lthimx/pnpbox1/freecad/magnet_support_main_arm/Capture d’écran du 2022-05-14 17-08-01.png

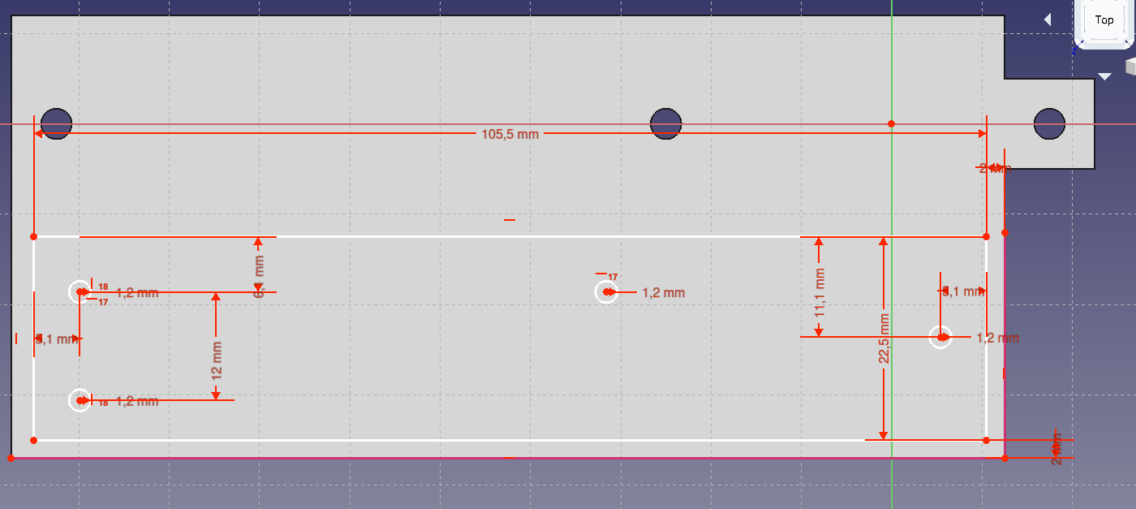
freecad/magnet_support_main_arm/Capture d’écran du 2022-05-14 17-08-01.png
