lthimx/pnpbox1/images/Capture d’écran du 2022-02-01 20-31-52.png

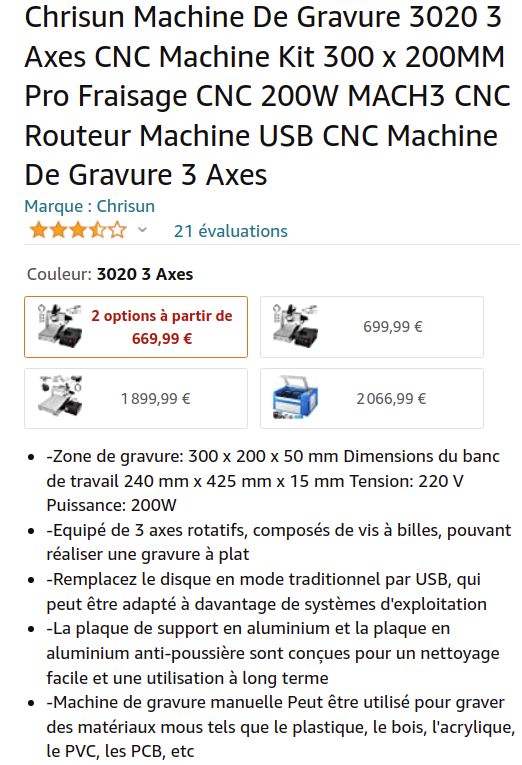
images/Capture d’écran du 2022-02-01 20-31-52.png
