lthimx/pnpbox1/openpnp/fidloc_template_18089185766861298502.png

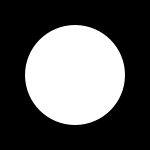
openpnp/fidloc_template_18089185766861298502.png
