lthimx/pnpbox1/freecad/magnet_support_main_arm/down_right_magnet_support_angle_arm.obj

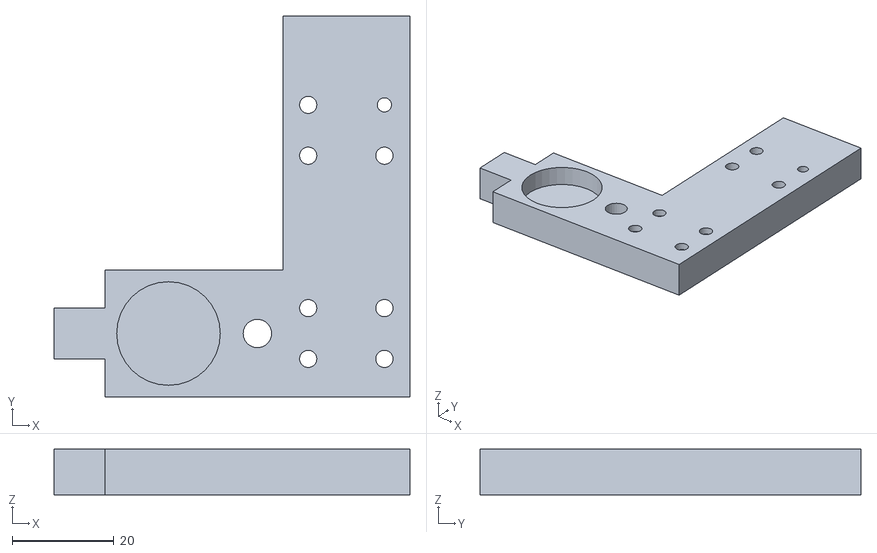
[picture p30: CAD file, 2022-06-12]
freecad/magnet_support_main_arm/down_right_magnet_support_angle_arm.obj
70.0 x 75.0 x 9.00
