lthimx/pnpbox1/freecad/reset_button/reset_unlock.obj

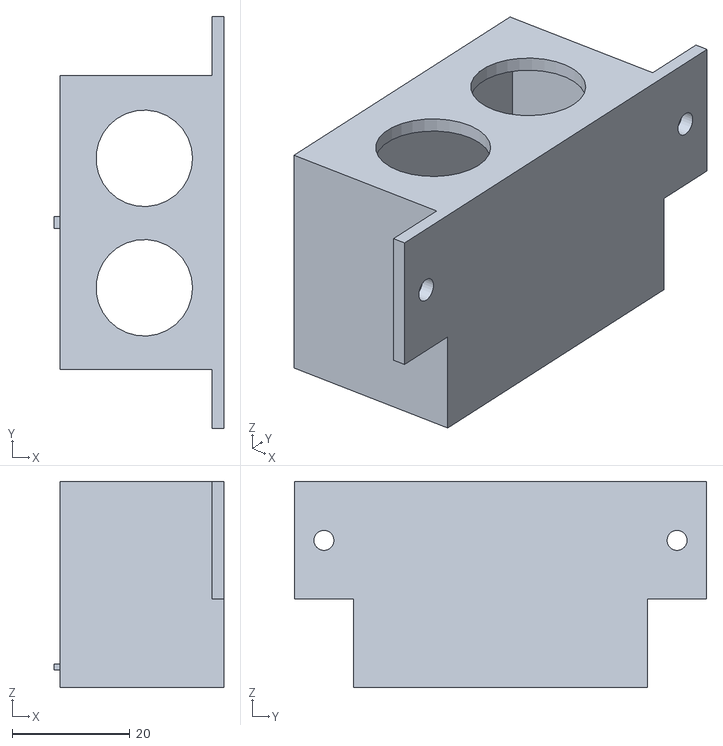
[picture p31: CAD file, 2022-04-11]
freecad/reset_button/reset_unlock.obj
28.8 x 70.0 x 35.0
