lthimx/pnpbox1/freecad/stl/acrylic_head_pnp_2.FCStd

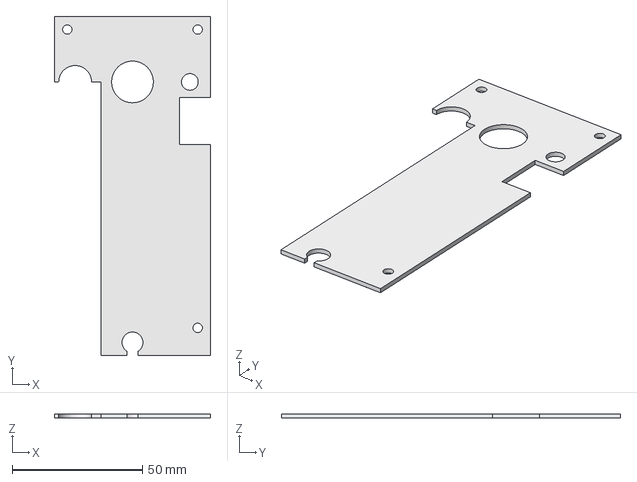
[picture p32: CAD file, 2022-04-11]
freecad/stl/acrylic_head_pnp_2.FCStd
60.0 x 130.0 x 1.60 mm
