lthimx/pnpbox1/freecad/usb_cam_case/usb_cam_case_up.FCStd

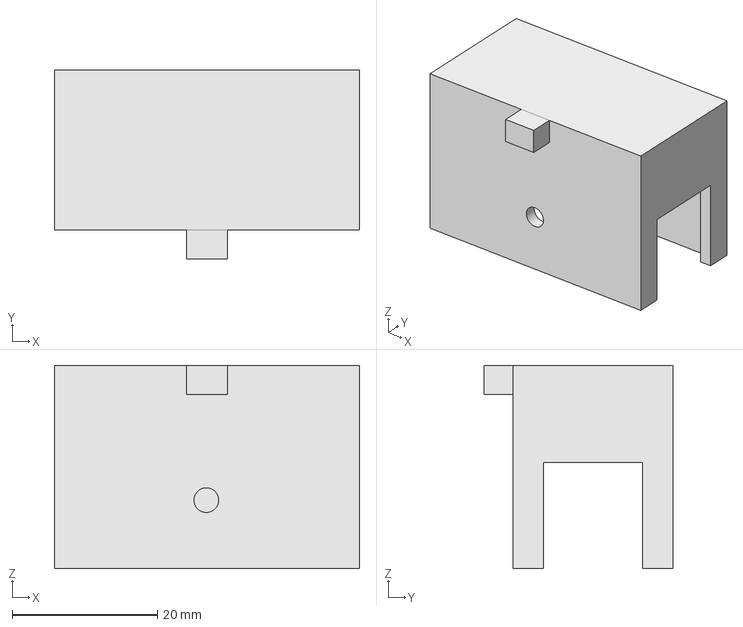
[picture p33: CAD file, 2022-06-12]
freecad/usb_cam_case/usb_cam_case_up.FCStd
42.0 x 26.0 x 28.0 mm
