lthimx/pnpbox1/freecad/magnet_support_main_arm/support_pump.FCStd

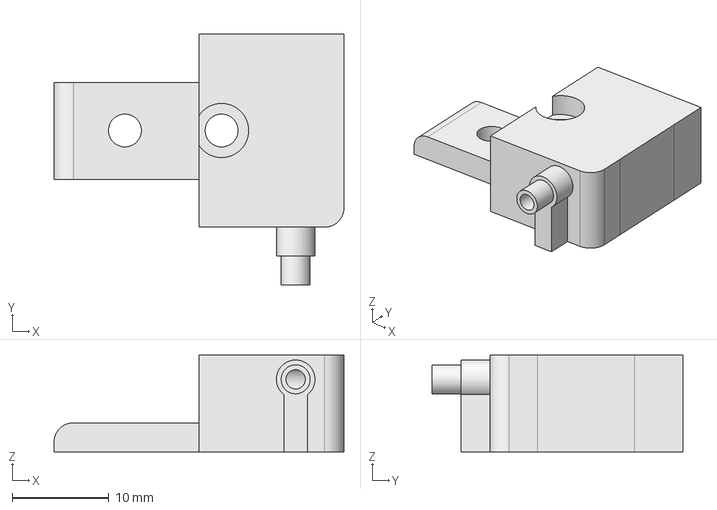
[picture p34: CAD file, 2022-06-12]
freecad/magnet_support_main_arm/support_pump.FCStd
30.0 x 26.0 x 10.0 mm
