lthimx/pnpbox1/freecad/reset_button/reset_unlock_button.FCStd

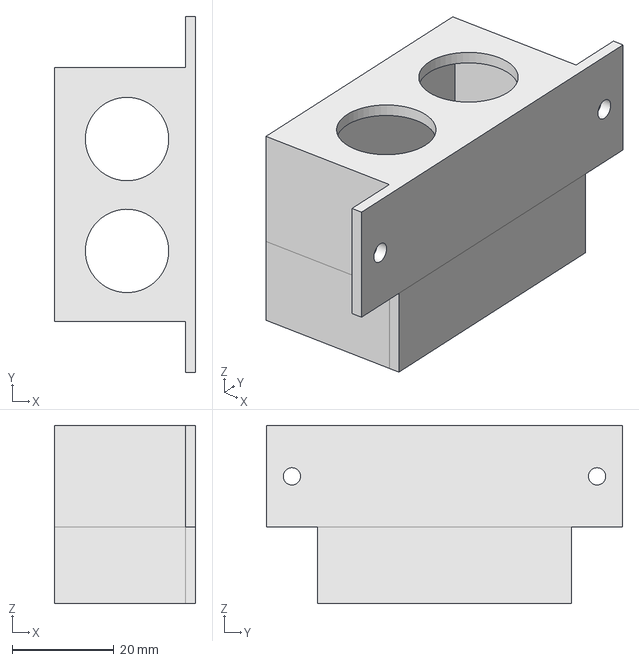
[picture p35: CAD file, 2022-04-11]
freecad/reset_button/reset_unlock_button.FCStd
27.8 x 70.0 x 35.0 mm
