lthimx/pnpbox1/freecad/magnet_support_main_arm/down_left_support_MGN9H.FCStd

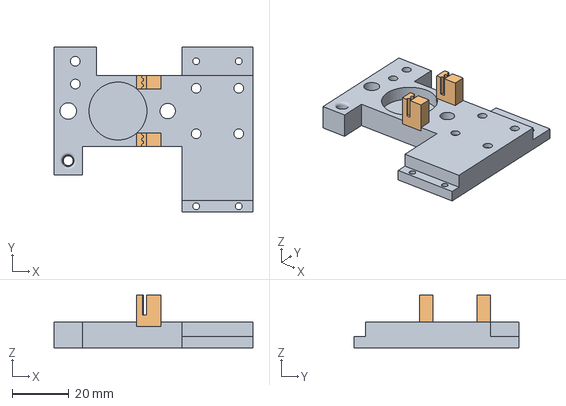
[picture p36: CAD file, 2022-06-12]
freecad/magnet_support_main_arm/down_left_support_MGN9H.FCStd
70.0 x 58.0 x 18.5 mm
belt_support_left001
