lthimx/pnpbox1/freecad/case_pnp/left_case_2_motore_conn.FCStd

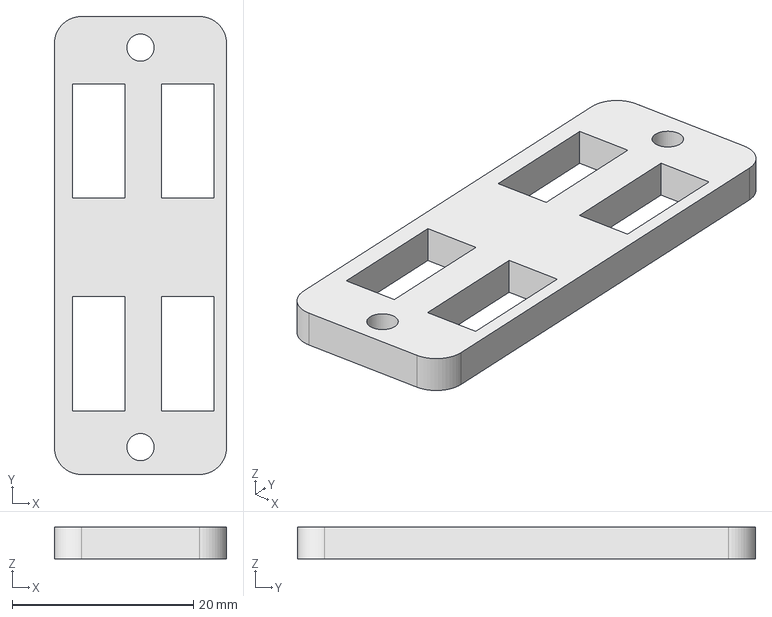
[picture p37: CAD file, 2021-10-03]
freecad/case_pnp/left_case_2_motore_conn.FCStd
19.0 x 50.5 x 3.50 mm
