lthimx/pnpbox1/freecad/magnet_support_main_arm/support_pcb_down_for_chain.FCStd

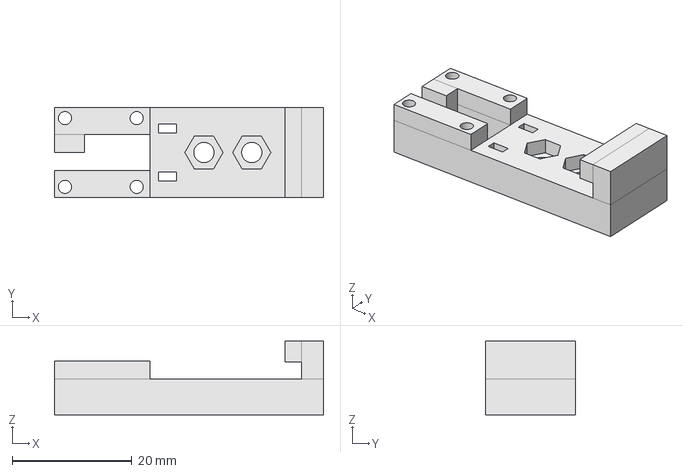
[picture p38: CAD file, 2022-06-12]
freecad/magnet_support_main_arm/support_pcb_down_for_chain.FCStd
45.0 x 15.0 x 12.3 mm
