lthimx/pnpbox1/freecad/stl/pnp_head_2.dxf

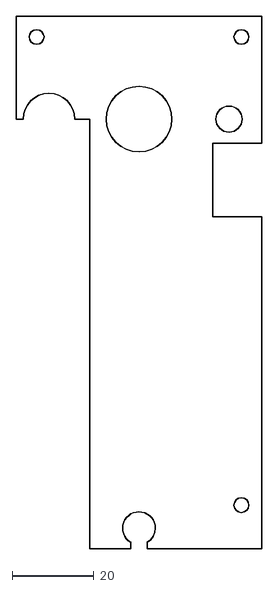
[picture p39: CAD file, 2022-03-26]
freecad/stl/pnp_head_2.dxf
60.0 x 130.0
