lthimx/pnpbox1/freecad/case_pnp/pump_supportV2.FCStd

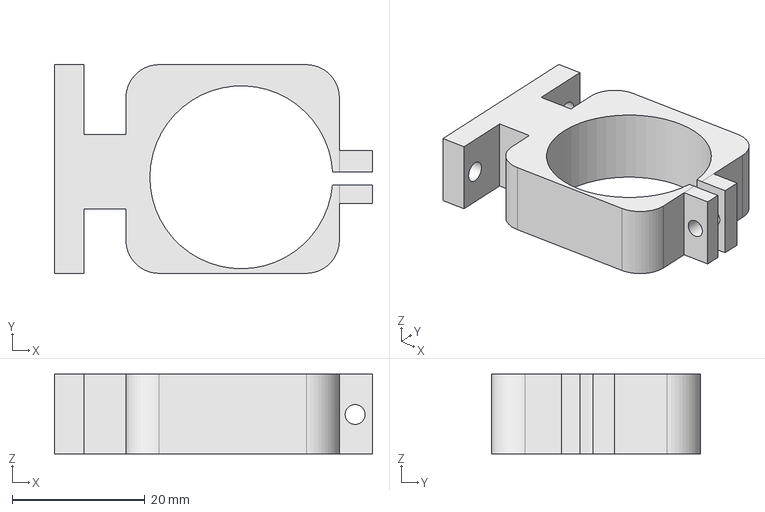
[picture p40: CAD file, 2021-10-03]
freecad/case_pnp/pump_supportV2.FCStd
48.0 x 31.5 x 12.0 mm
