lthimx/pnpbox1/freecad/magnet_support_main_arm/up_left_magnet_arm_with_pcb_support.FCStd

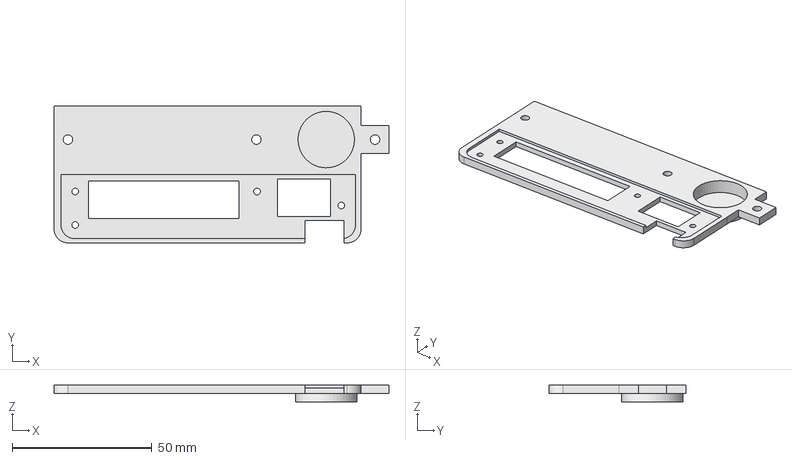
[picture p41: CAD file, 2022-06-12]
freecad/magnet_support_main_arm/up_left_magnet_arm_with_pcb_support.FCStd
120.0 x 49.0 x 6.00 mm
