lthimx/pnpbox1/freecad/stl/test_ironing.obj

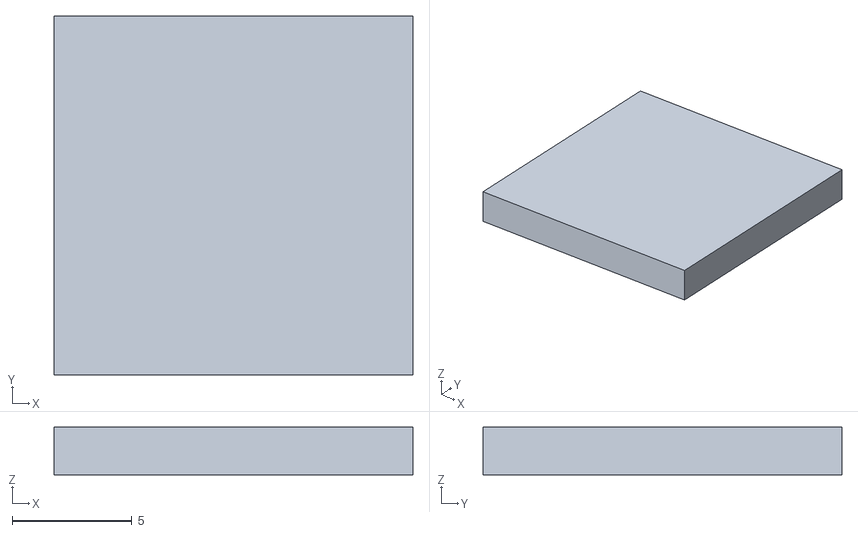
[picture p42: CAD file, 2022-03-26]
freecad/stl/test_ironing.obj
15.0 x 15.0 x 2.00
