lthimx/pnpbox1/freecad/case_pnp/pnp_support_hifive.obj

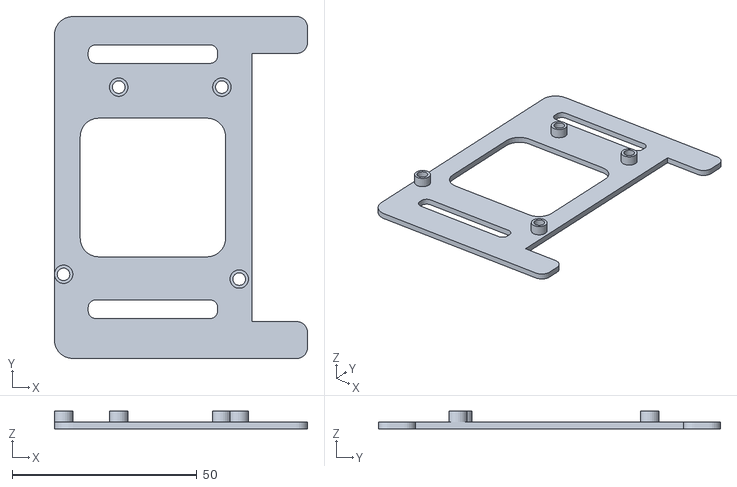
[picture p43: CAD file, 2021-10-03]
freecad/case_pnp/pnp_support_hifive.obj
68.5 x 92.5 x 4.80
