lthimx/pnpbox1/freecad/magnet_support_main_arm/down_left_magnet_with_pcb_support.obj

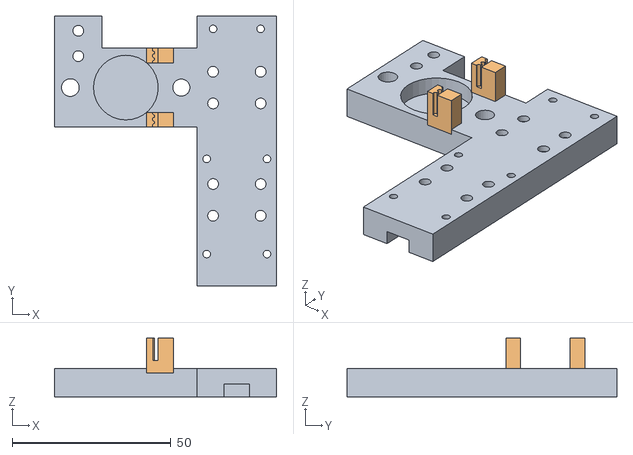
[picture p44: CAD file, 2022-06-12]
freecad/magnet_support_main_arm/down_left_magnet_with_pcb_support.obj
70.0 x 85.0 x 18.5
belt_support_left001
