lthimx/pnpbox1/freecad/magnet_support_main_arm/up_right_magnet_support_arm.FCStd

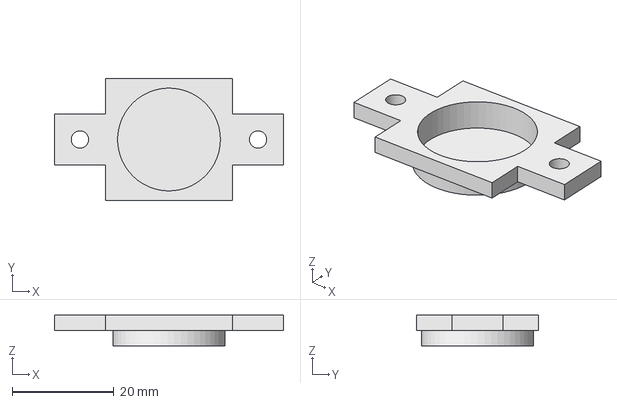
[picture p45: CAD file, 2022-06-12]
freecad/magnet_support_main_arm/up_right_magnet_support_arm.FCStd
45.0 x 24.0 x 6.00 mm
