lthimx/pnpbox1/freecad/simplePnP/support_for_fixed_head.FCStd

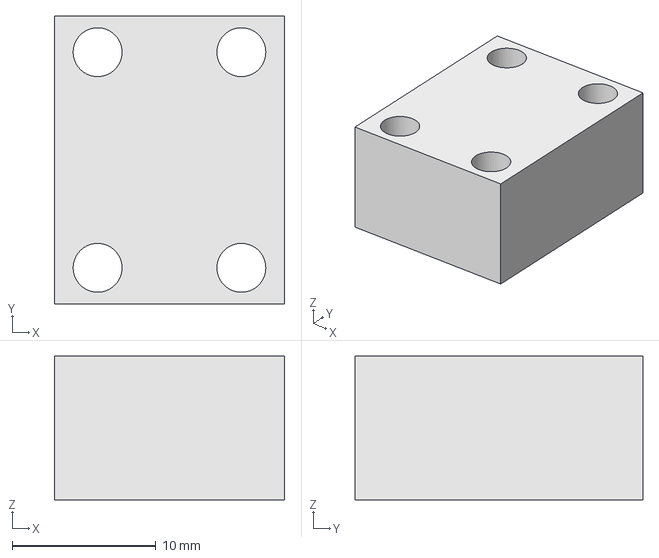
[picture p46: CAD file, 2022-01-29]
freecad/simplePnP/support_for_fixed_head.FCStd
16.0 x 20.0 x 10.0 mm
