lthimx/pnpbox1/freecad/case_pnp/pnp_case_right.obj

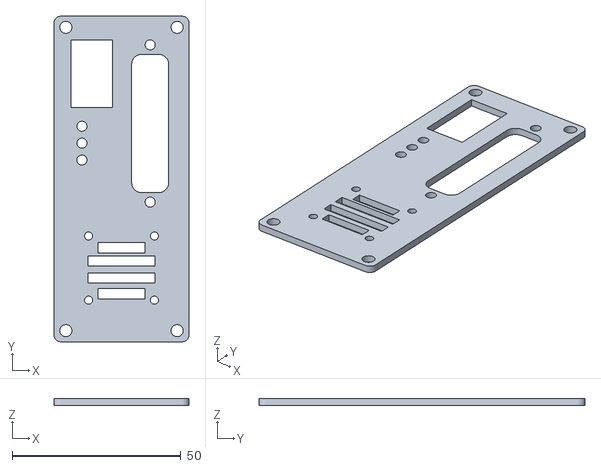
[picture p47: CAD file, 2021-10-03]
freecad/case_pnp/pnp_case_right.obj
40.0 x 96.5 x 2.00
