lthimx/pnpbox1/freecad/magnet_support_main_arm/up_left_magnet_support_2.obj

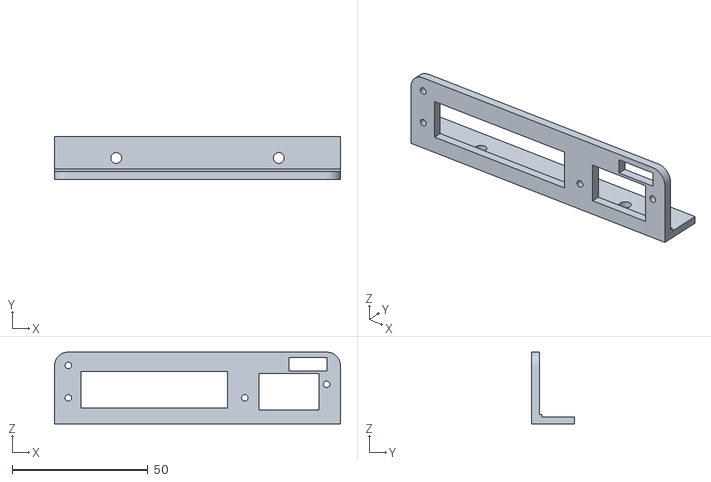
[picture p48: CAD file, 2022-06-12]
freecad/magnet_support_main_arm/up_left_magnet_support_2.obj
105.5 x 16.0 x 26.5
