lthimx/pnpbox1/freecad/simplePnP/test_adapter_pneumatique.obj

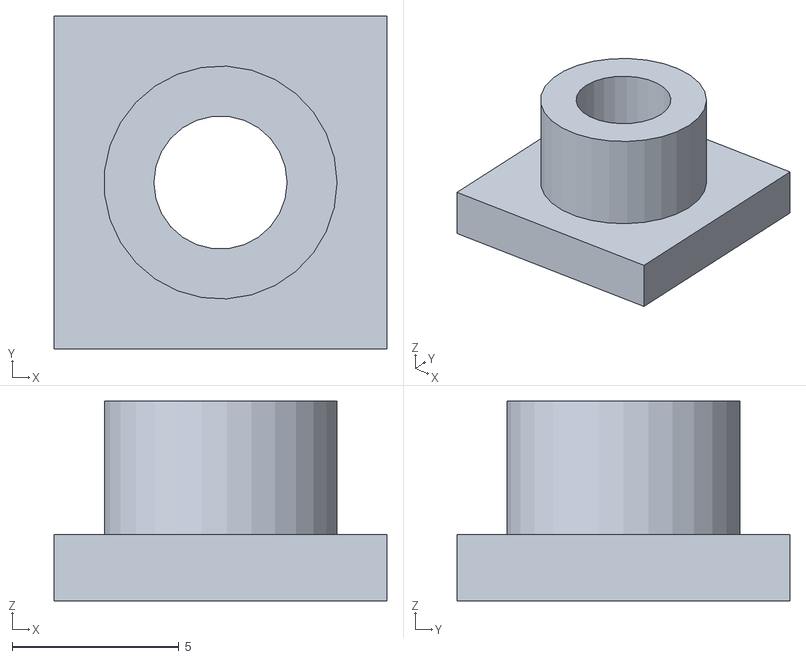
[picture p49: CAD file, 2022-01-29]
freecad/simplePnP/test_adapter_pneumatique.obj
10.0 x 10.0 x 6.00
