lthimx/pnpbox1/freecad/case_pnp/bute_arduino.FCStd

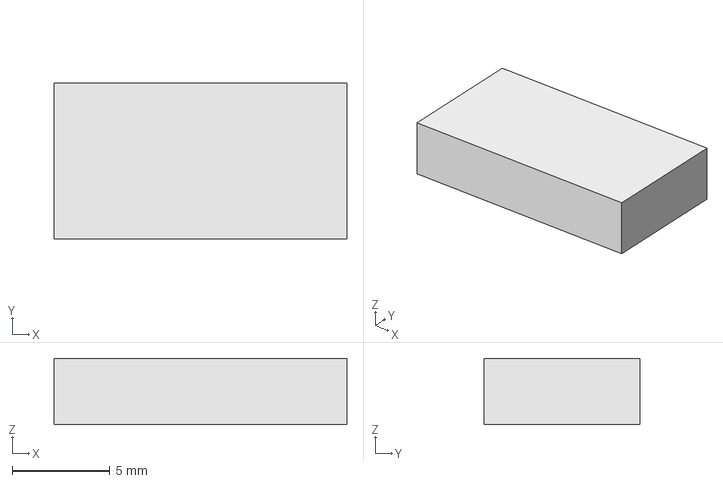
[picture p50: CAD file, 2021-10-03]
freecad/case_pnp/bute_arduino.FCStd
15.0 x 8.00 x 3.40 mm
