lthimx/pnpbox1/freecad/magnet_support_main_arm/belt_support_left.FCStd

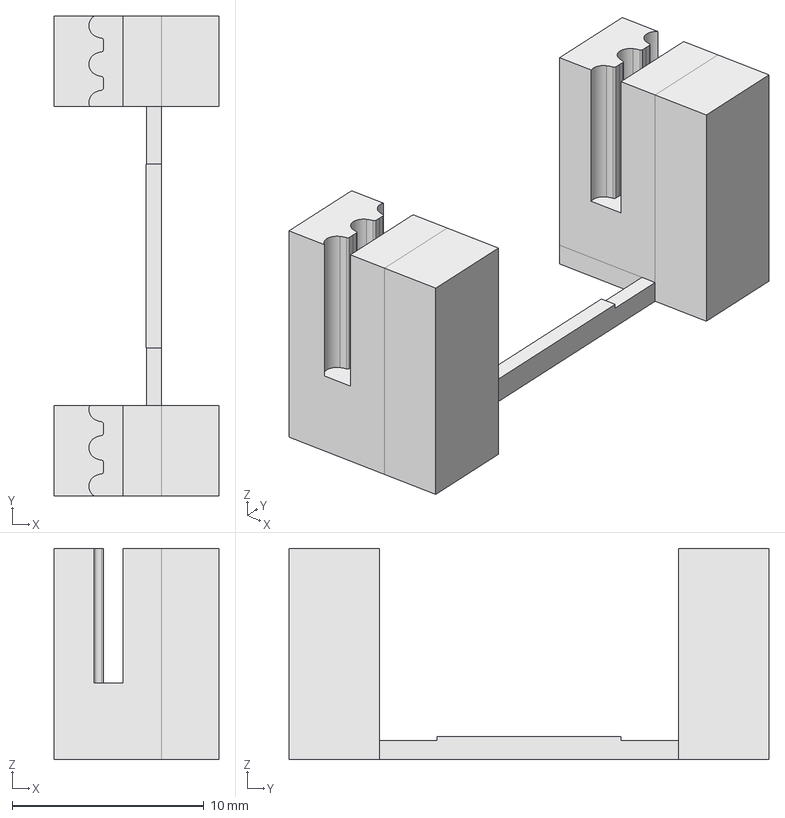
[picture p51: CAD file, 2022-06-12]
freecad/magnet_support_main_arm/belt_support_left.FCStd
8.60 x 25.0 x 11.0 mm
