lthimx/pnpbox1/freecad/magnet_support_main_arm/down_left_magnet_arm_bak.FCStd

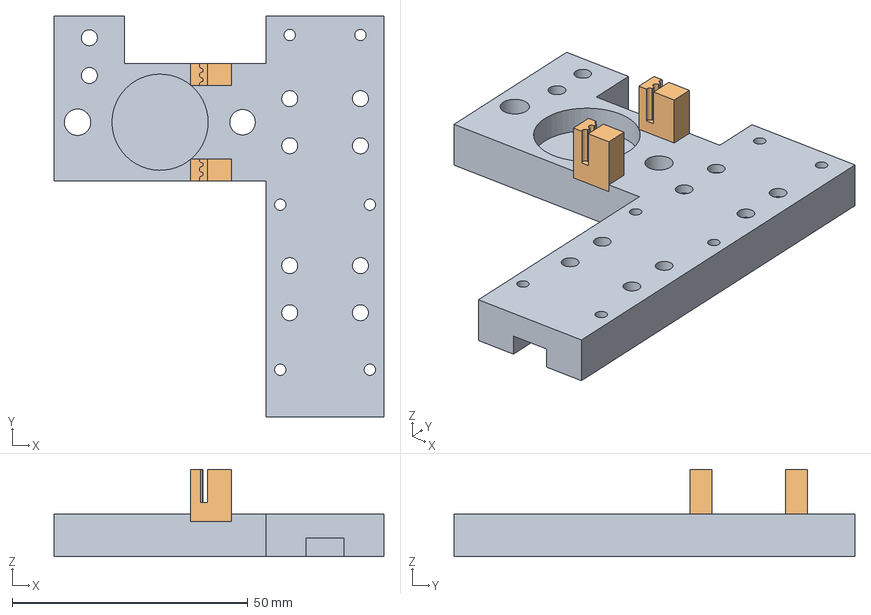
[picture p52: CAD file, 2022-06-12]
freecad/magnet_support_main_arm/down_left_magnet_arm_bak.FCStd
70.0 x 85.0 x 18.5 mm
belt_support_left001
