lthimx/pnpbox1/freecad/simplePnP/test_pneumatique_adapter.obj

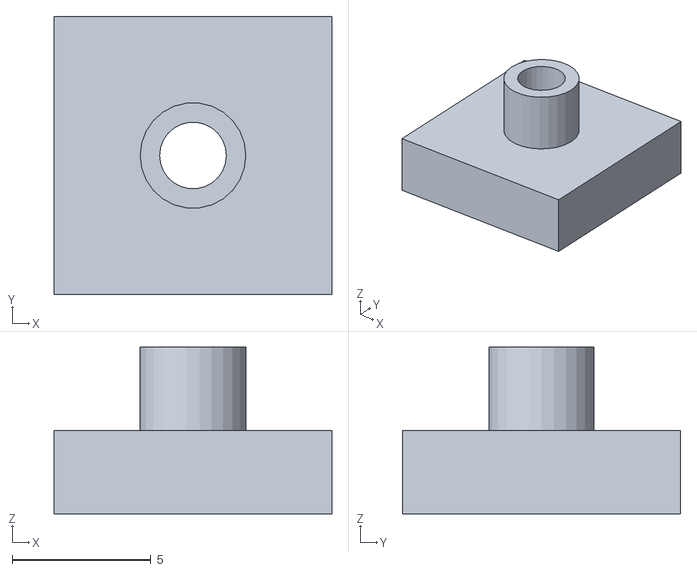
[picture p53: CAD file, 2022-01-29]
freecad/simplePnP/test_pneumatique_adapter.obj
10.0 x 10.0 x 6.00
