lthimx/pnpbox1/freecad/case_pnp/support_pump.obj

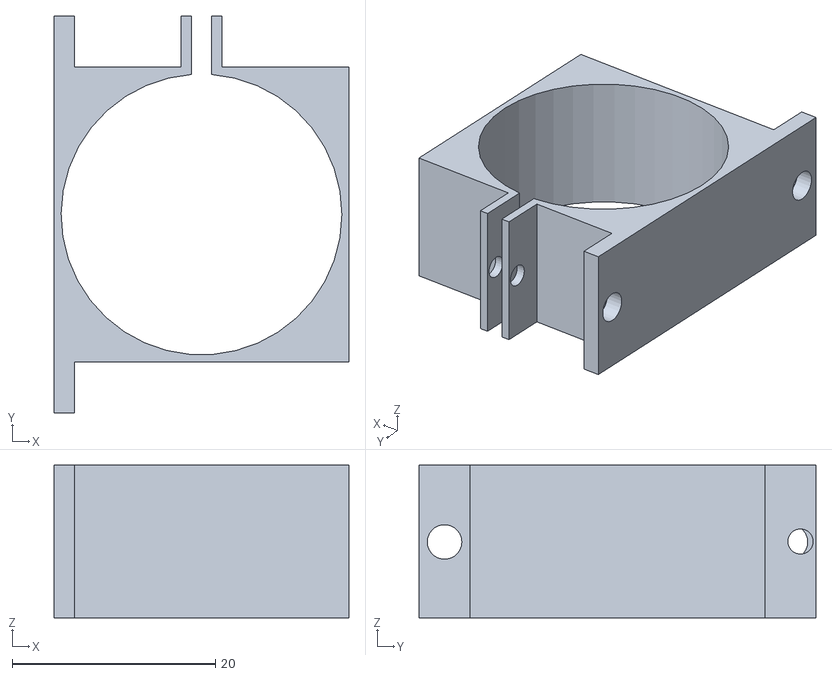
[picture p54: CAD file, 2021-10-03]
freecad/case_pnp/support_pump.obj
29.0 x 39.0 x 15.0
