lthimx/pnpbox1/freecad/case_pnp/pnp_case_left_motor_conn.obj

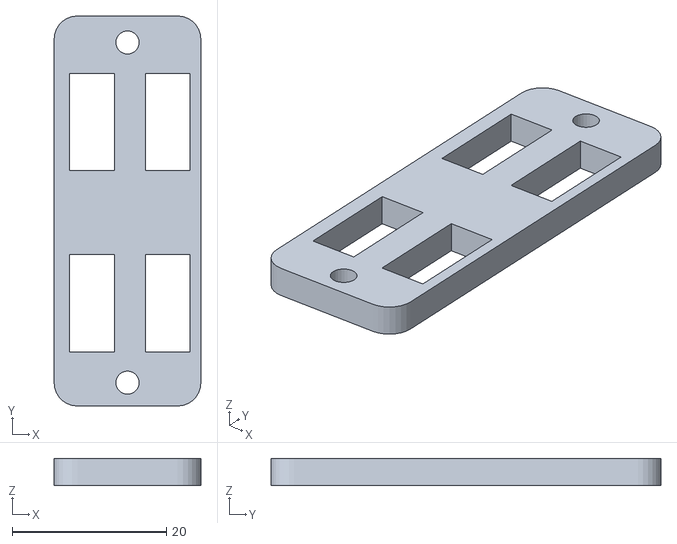
[picture p55: CAD file, 2021-10-03]
freecad/case_pnp/pnp_case_left_motor_conn.obj
19.0 x 50.5 x 3.50
