lthimx/pnpbox1/freecad/magnet_support_main_arm/down_right_support_MGN9H.obj

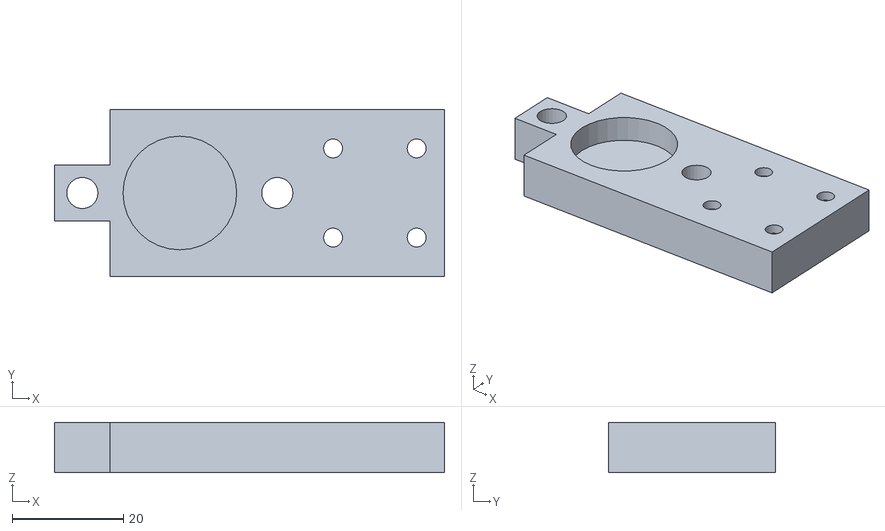
[picture p56: CAD file, 2022-06-12]
freecad/magnet_support_main_arm/down_right_support_MGN9H.obj
70.0 x 30.0 x 9.00
