lthimx/pnpbox1/freecad/case_pnp/pump_support.FCStd

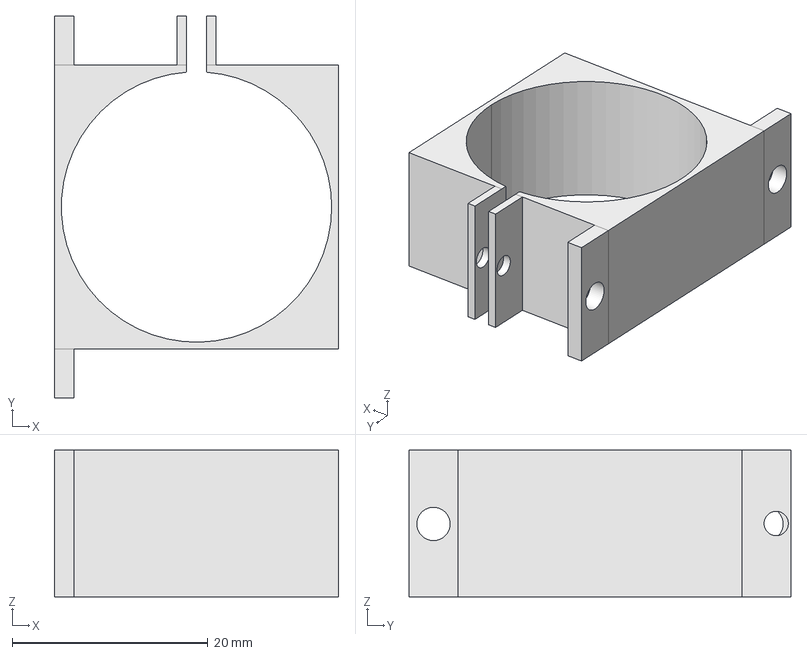
[picture p57: CAD file, 2021-10-03]
freecad/case_pnp/pump_support.FCStd
29.0 x 39.0 x 15.0 mm
