lthimx/pnpbox1/freecad/magnet_support_main_arm/support_pcb_down_for_chain_0.obj

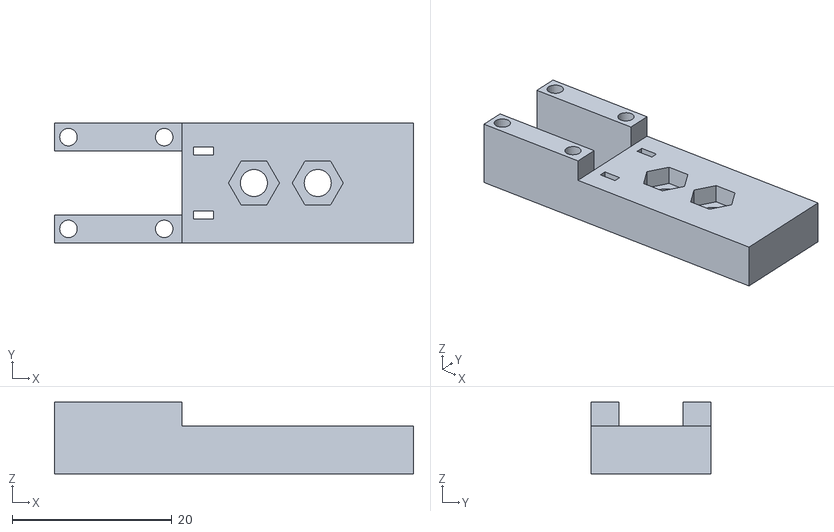
[picture p58: CAD file, 2022-06-12]
freecad/magnet_support_main_arm/support_pcb_down_for_chain_0.obj
45.0 x 15.0 x 9.00
