lthimx/pnpbox1/freecad/simplePnP/pump_cable_adapter.obj

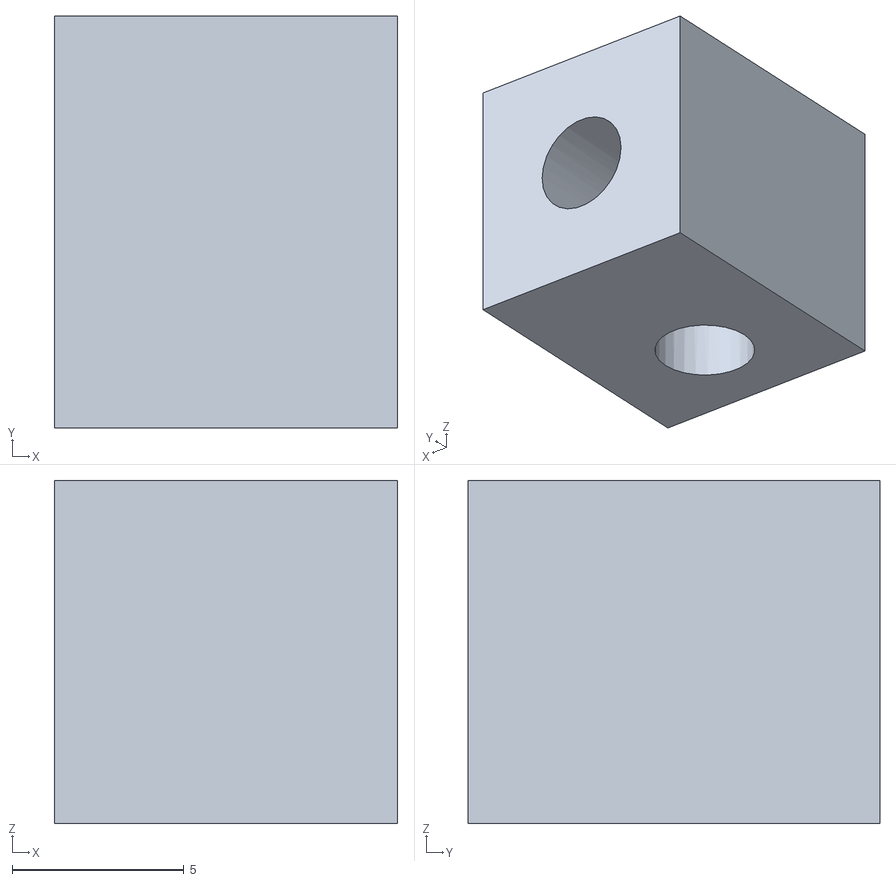
[picture p59: CAD file, 2022-01-29]
freecad/simplePnP/pump_cable_adapter.obj
10.0 x 12.0 x 10.0
