lthimx/pnpbox1/freecad/case_pnp/left_case.FCStd

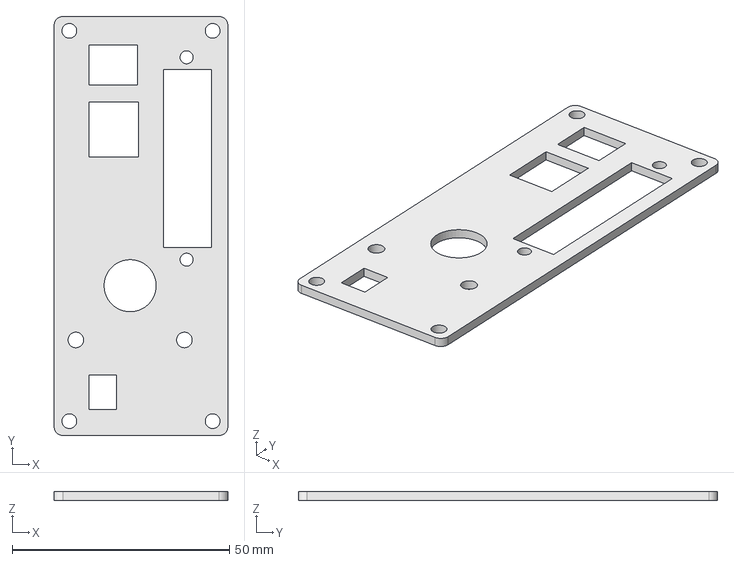
[picture p60: CAD file, 2021-10-03]
freecad/case_pnp/left_case.FCStd
40.0 x 96.5 x 2.00 mm
