lthimx/pnpbox1/freecad/magnet_support_main_arm/down_right_magnet_arm_support.FCStd

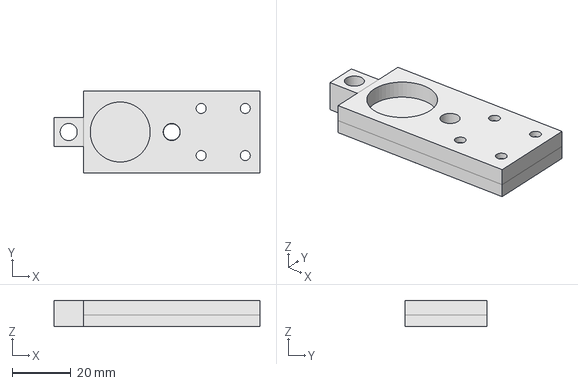
[picture p61: CAD file, 2022-06-12]
freecad/magnet_support_main_arm/down_right_magnet_arm_support.FCStd
70.0 x 28.0 x 9.00 mm
