lthimx/pnpbox1/freecad/case_pnp/cale_arduino.obj

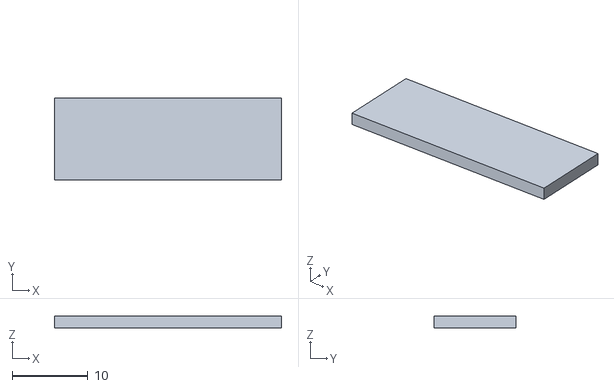
[picture p62: CAD file, 2021-10-03]
freecad/case_pnp/cale_arduino.obj
30.0 x 10.8 x 1.60
