lthimx/pnpbox1/freecad/magnet_support_main_arm/right_magnet_arm_2.obj

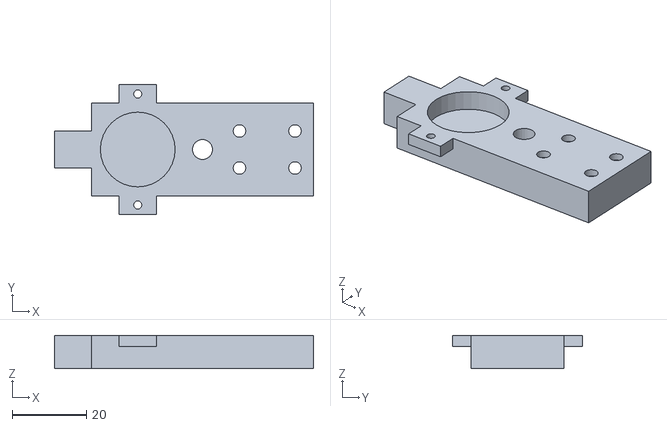
[picture p63: CAD file, 2022-06-12]
freecad/magnet_support_main_arm/right_magnet_arm_2.obj
70.0 x 35.0 x 9.00
