lthimx/pnpbox1/freecad/case_pnp/hifive_support.FCStd

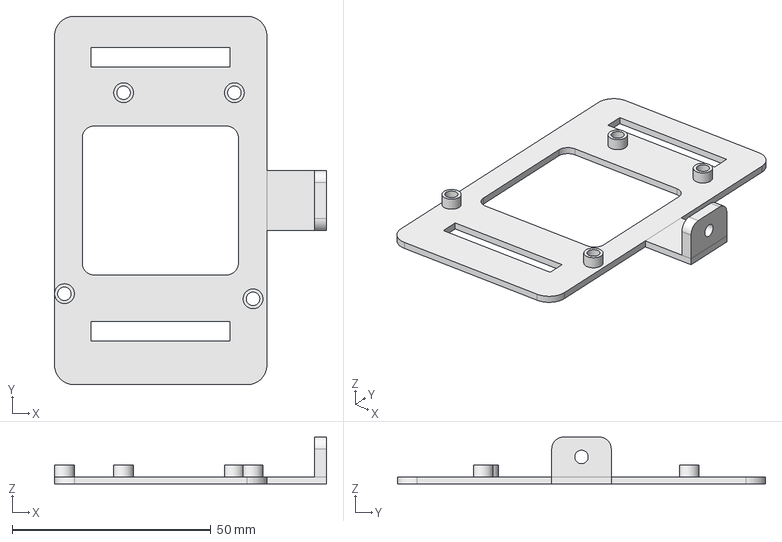
[picture p64: CAD file, 2021-10-03]
freecad/case_pnp/hifive_support.FCStd
68.5 x 92.8 x 11.8 mm
