lthimx/pnpbox1/freecad/magnet_support_main_arm/up_left_magnet_pcb_spport_2.FCStd

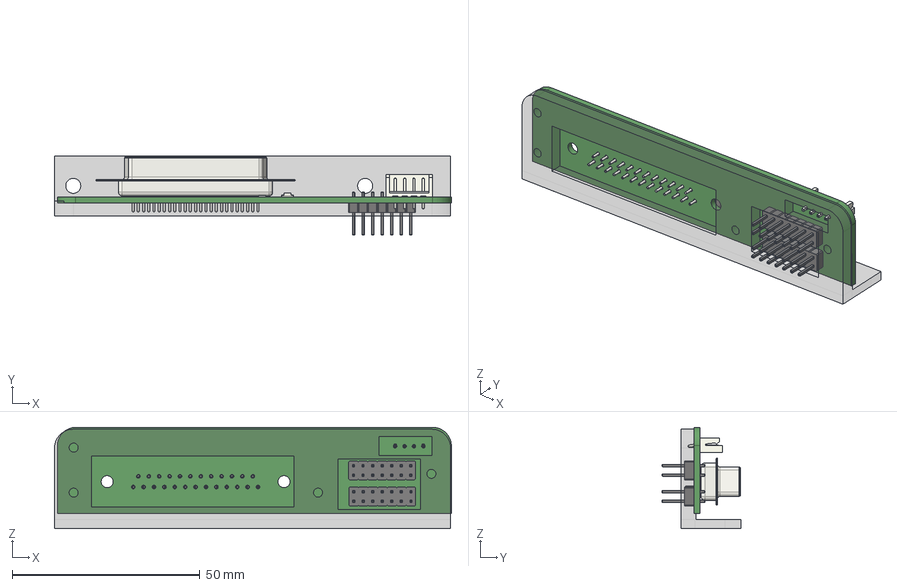
[picture p65: CAD file, 2022-06-12]
freecad/magnet_support_main_arm/up_left_magnet_pcb_spport_2.FCStd
105.8 x 21.1 x 27.0 mm
Pcb_64d6
D3_LED_1206_3216Metric_627807AB
J1_DSUB-25_Female_Vertical_P2.77x2.84mm_MountingHoles_627807F2
R3_R_0805_2012Metric_6278086D
J4_JST_B4B_EH_A_62780C6B
J2_PinHeader_2x07_P254mm_Vertical_62780816
J3_PinHeader_2x07_P254mm_Vertical_6278083A
