lthimx/pnpbox1/freecad/case_pnp/pnp_case_left_test.obj

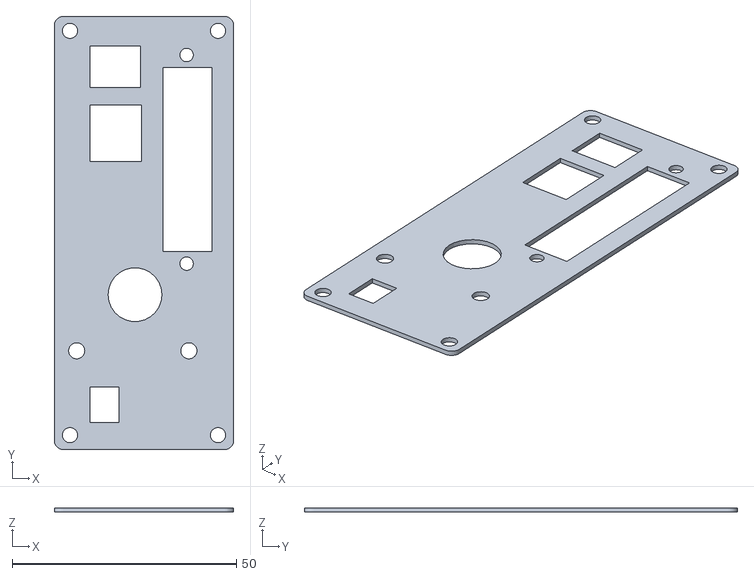
[picture p66: CAD file, 2021-10-03]
freecad/case_pnp/pnp_case_left_test.obj
40.0 x 96.5 x 1.00
