lthimx/pnpbox1/freecad/simplePnP/support_for_drag_chain_on_fixed_head.obj

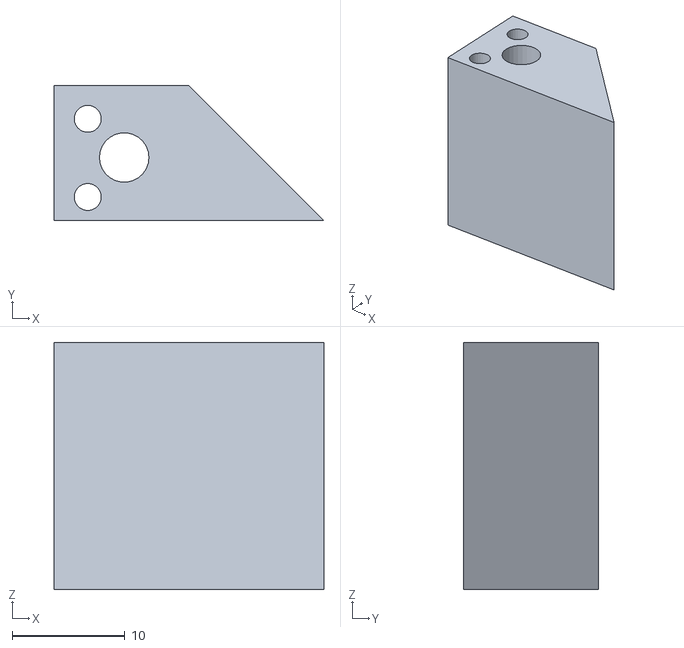
[picture p67: CAD file, 2022-01-20]
freecad/simplePnP/support_for_drag_chain_on_fixed_head.obj
24.0 x 12.0 x 22.0
