lthimx/pnpbox1/freecad/simplePnP/ring_for_nema8.FCStd

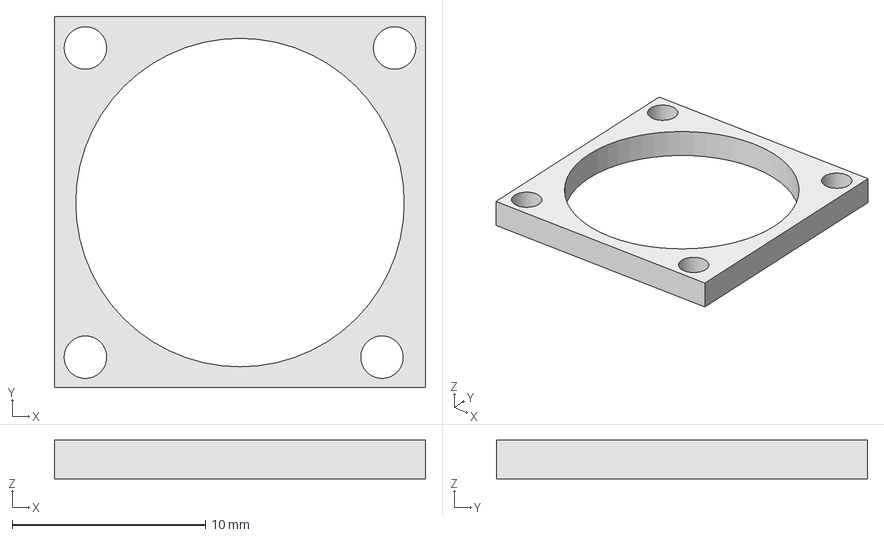
[picture p68: CAD file, 2022-01-20]
freecad/simplePnP/ring_for_nema8.FCStd
19.2 x 19.2 x 2.00 mm
