lthimx/pnpbox1/freecad/simplePnP/belt_general.obj

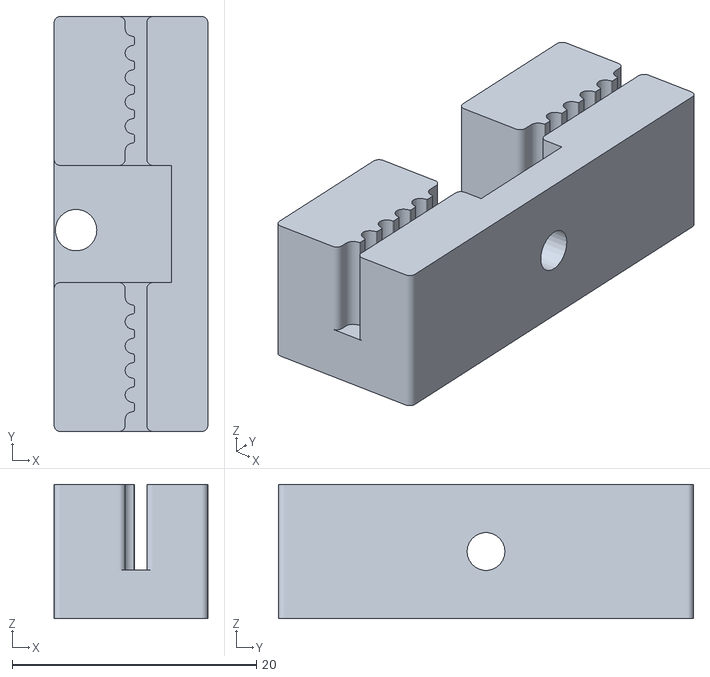
[picture p69: CAD file, 2022-01-20]
freecad/simplePnP/belt_general.obj
12.6 x 34.0 x 11.0
