lthimx/pnpbox1/freecad/simplePnP/for_fixing_drag_chain_on_head.FCStd

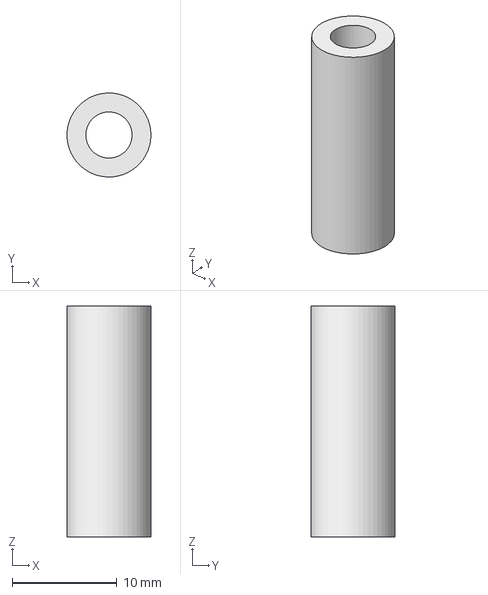
[picture p70: CAD file, 2022-01-20]
freecad/simplePnP/for_fixing_drag_chain_on_head.FCStd
7.99 x 8.00 x 22.0 mm
