lthimx/pnpbox1/freecad/simplePnP/support_for_camera.FCStd

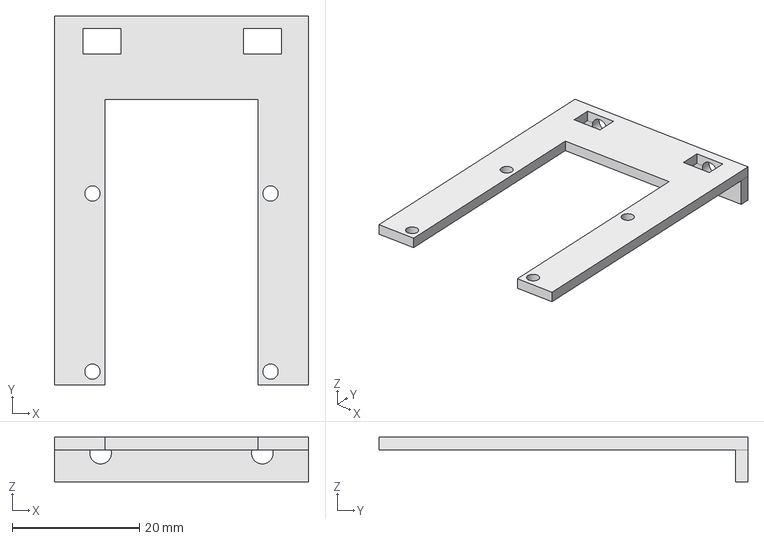
[picture p71: CAD file, 2022-01-20]
freecad/simplePnP/support_for_camera.FCStd
40.0 x 58.0 x 7.00 mm
