lthimx/pnpbox1/freecad/simplePnP/support_for_grag_chain_on_fixed_head.FCStd

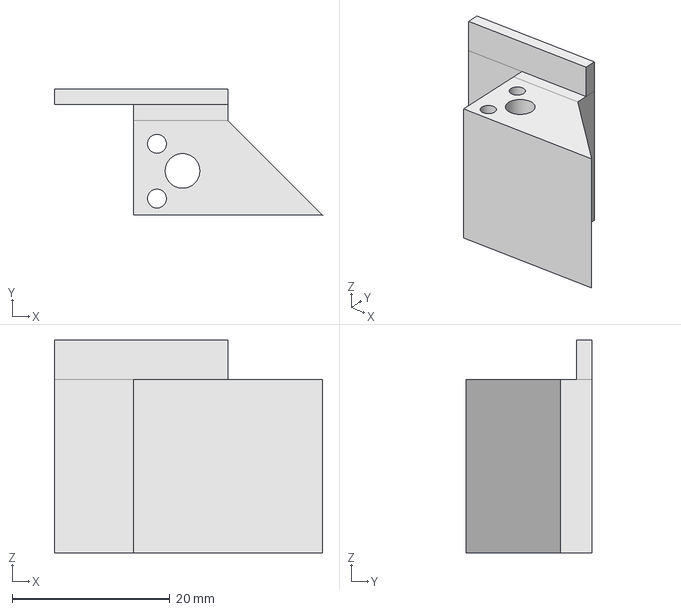
[picture p72: CAD file, 2022-01-20]
freecad/simplePnP/support_for_grag_chain_on_fixed_head.FCStd
34.0 x 16.0 x 27.0 mm
