lthimx/pnpbox1/freecad/simplePnP/support_camera.obj

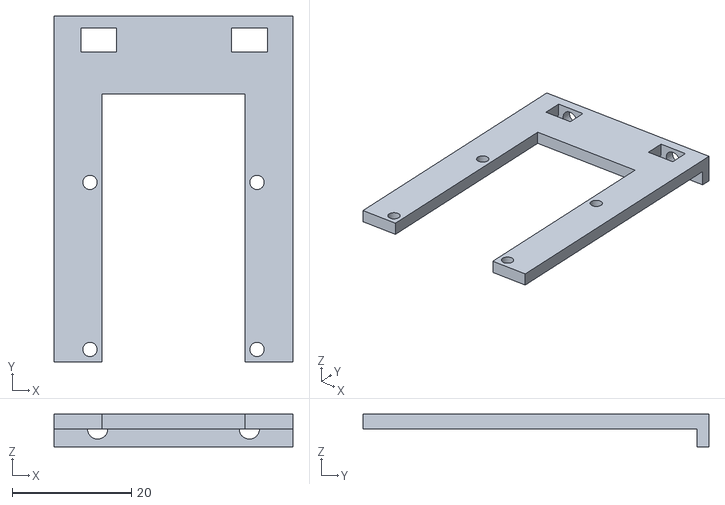
[picture p73: CAD file, 2022-01-20]
freecad/simplePnP/support_camera.obj
40.0 x 58.0 x 5.50
