lthimx/pnpbox1/freecad/simplePnP/rondelle_visM5.FCStd

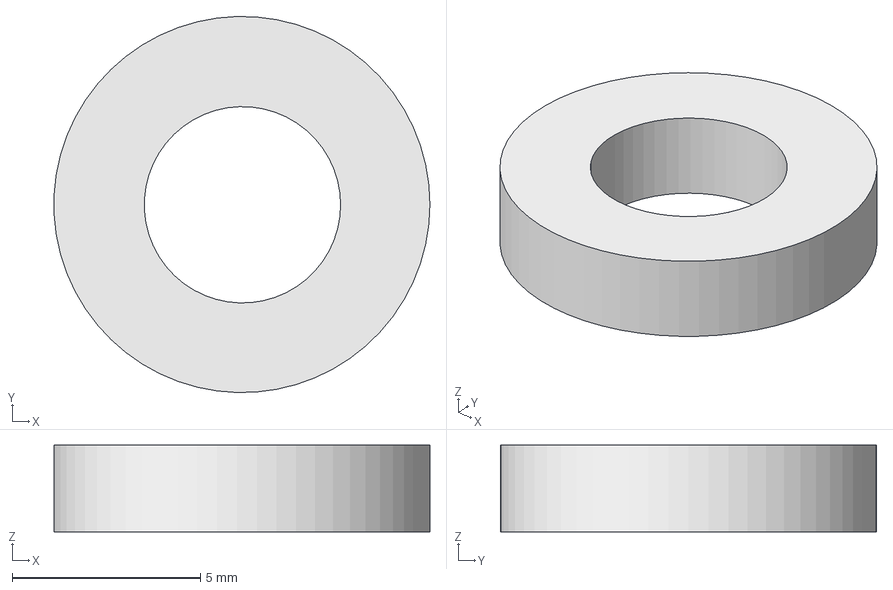
[picture p74: CAD file, 2021-10-03]
freecad/simplePnP/rondelle_visM5.FCStd
9.99 x 10.00 x 2.30 mm
