lthimx/pnpbox1/freecad/simplePnP/ajust_drag_chain_pilone.FCStd

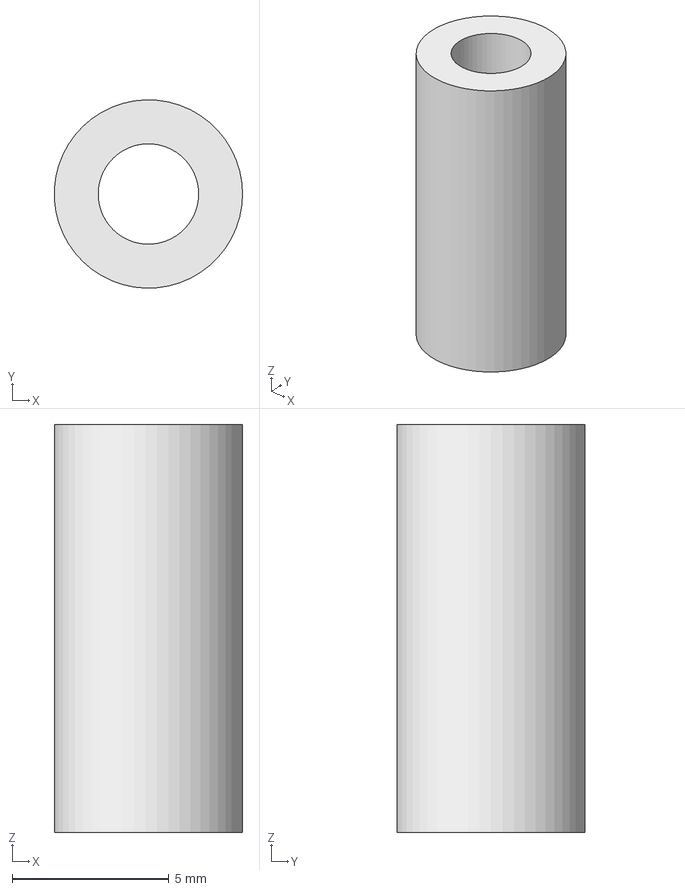
[picture p75: CAD file, 2021-10-03]
freecad/simplePnP/ajust_drag_chain_pilone.FCStd
5.99 x 6.00 x 13.0 mm
