lthimx/pnpbox1/freecad/simplePnP/support_nema8_right.FCStd

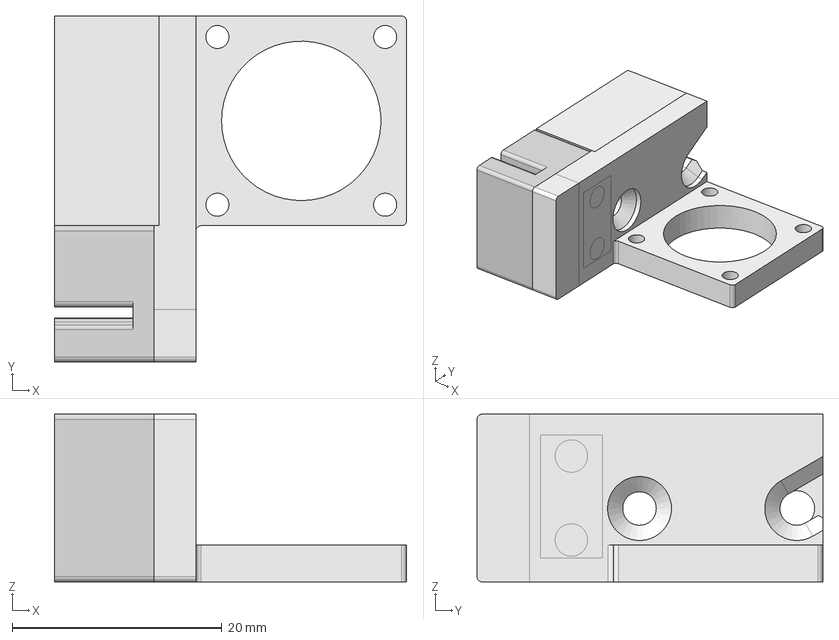
[picture p76: CAD file, 2021-10-03]
freecad/simplePnP/support_nema8_right.FCStd
33.6 x 33.0 x 16.0 mm
FusionComponent001
