lthimx/pnpbox1/freecad/simplePnP/end_course_Y_bottom.FCStd

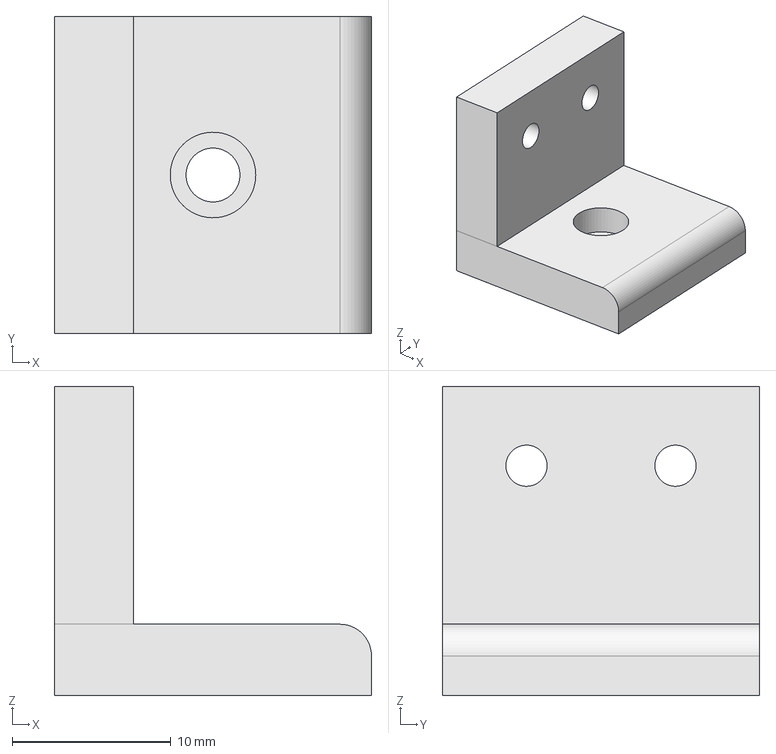
[picture p77: CAD file, 2021-10-03]
freecad/simplePnP/end_course_Y_bottom.FCStd
20.0 x 20.0 x 19.5 mm
