lthimx/pnpbox1/freecad/simplePnP/ecrou_fixation_jetson_nano.FCStd

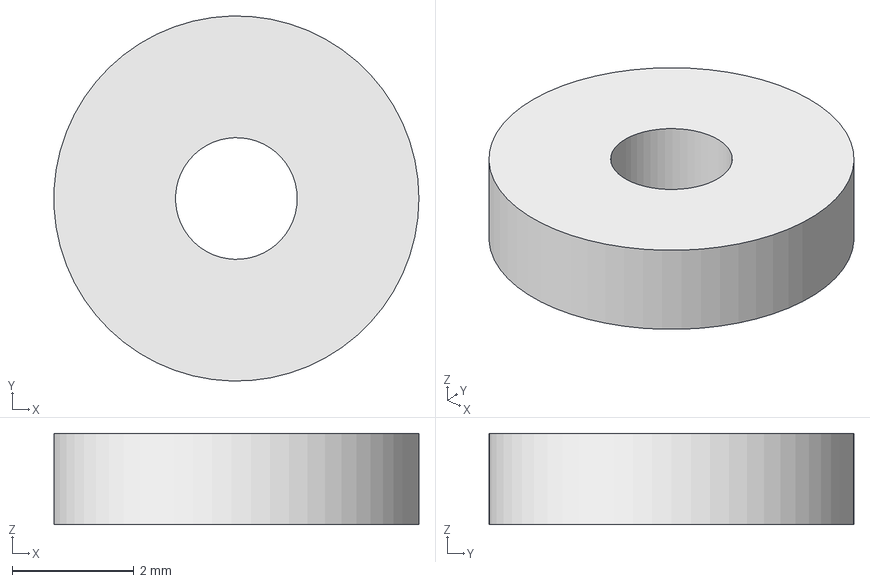
[picture p78: CAD file, 2021-10-03]
freecad/simplePnP/ecrou_fixation_jetson_nano.FCStd
6.00 x 6.00 x 1.50 mm
