lthimx/pnpbox1/freecad/simplePnP/bute_2.FCStd

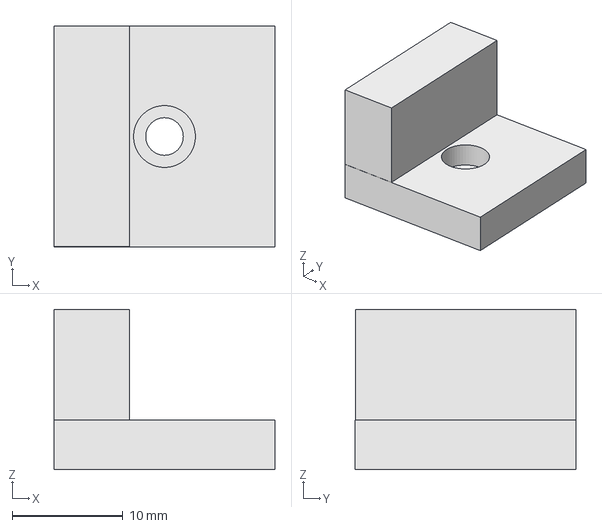
[picture p79: CAD file, 2021-10-03]
freecad/simplePnP/bute_2.FCStd
20.0 x 20.0 x 14.5 mm
