lthimx/pnpbox1/freecad/simplePnP/poulie_left_support.obj

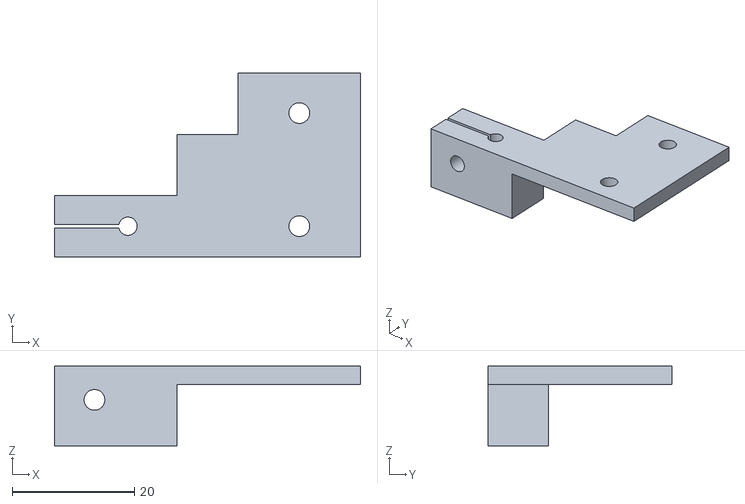
[picture p80: CAD file, 2021-10-03]
freecad/simplePnP/poulie_left_support.obj
50.0 x 30.0 x 13.0
