lthimx/pnpbox1/freecad/simplePnP/jetson_nano_support_dessous.obj

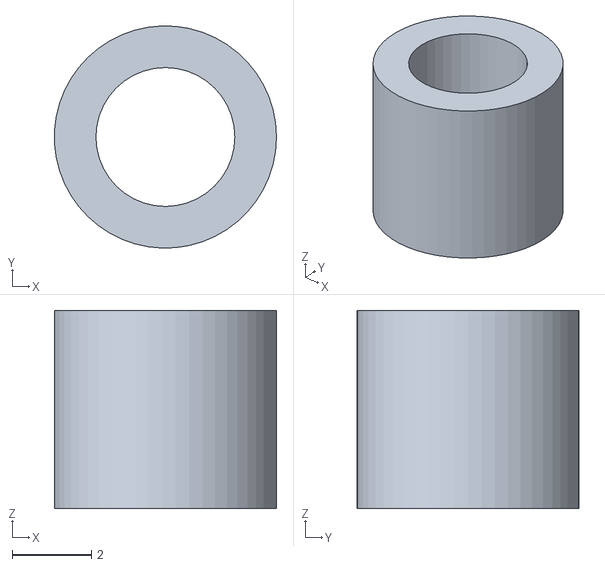
[picture p81: CAD file, 2021-10-03]
freecad/simplePnP/jetson_nano_support_dessous.obj
5.59 x 5.60 x 5.00
