lthimx/pnpbox1/freecad/simplePnP/left_support_for_drag_chain.FCStd

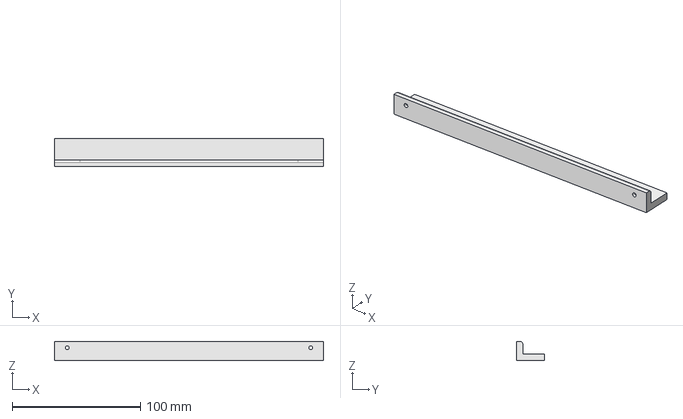
[picture p82: CAD file, 2021-10-03]
freecad/simplePnP/left_support_for_drag_chain.FCStd
210.0 x 22.0 x 15.0 mm
