lthimx/pnpbox1/freecad/simplePnP/belt_clamp_right.obj

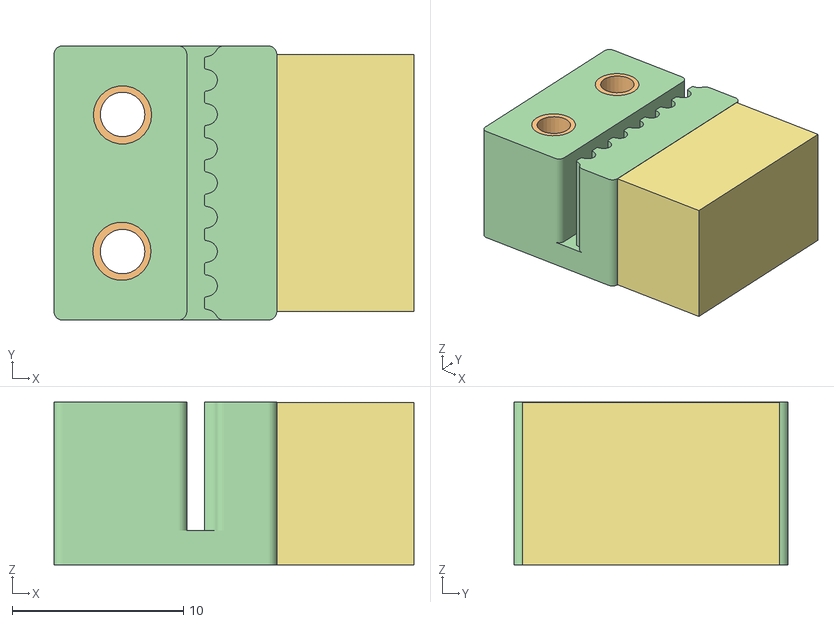
[picture p83: CAD file, 2021-10-03]
freecad/simplePnP/belt_clamp_right.obj
21.0 x 16.0 x 9.50
FusionComponent
BaseFeature
