lthimx/pnpbox1/freecad/simplePnP/support_nema8_left.FCStd

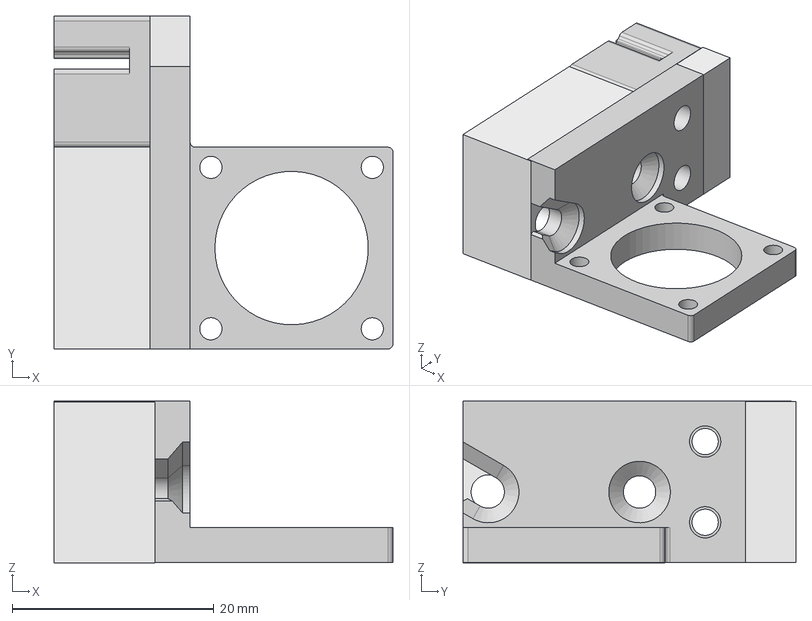
[picture p84: CAD file, 2021-10-03]
freecad/simplePnP/support_nema8_left.FCStd
33.6 x 33.0 x 16.0 mm
FusionComponent
FusionComponent001
