lthimx/pnpbox1/freecad/simplePnP/end_course_actuator.obj

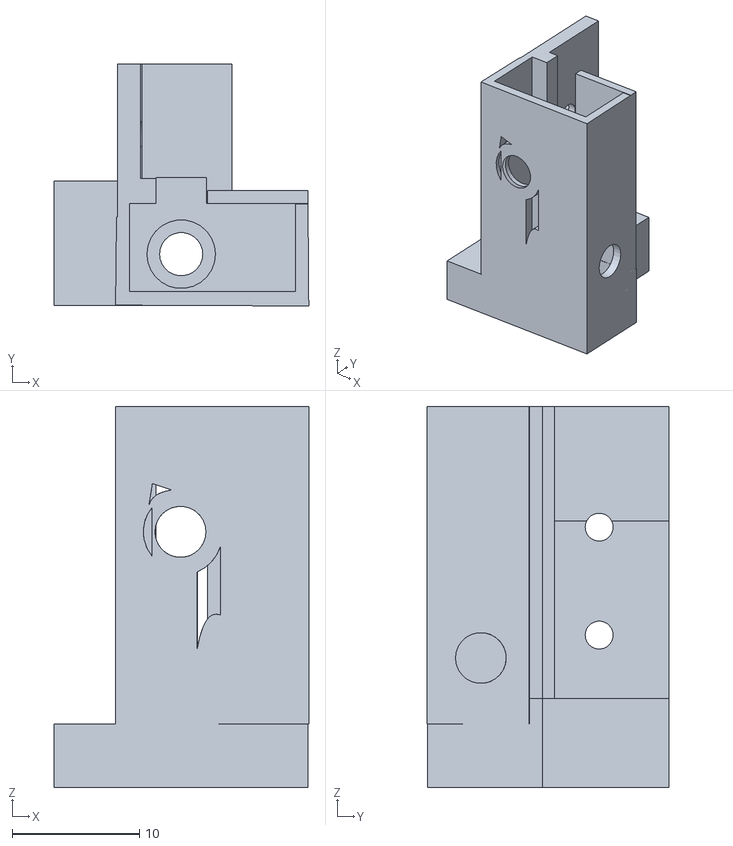
[picture p85: CAD file, 2021-10-03]
freecad/simplePnP/end_course_actuator.obj
20.0 x 19.1 x 30.0
