lthimx/pnpbox1/freecad/simplePnP/rehausseur.obj

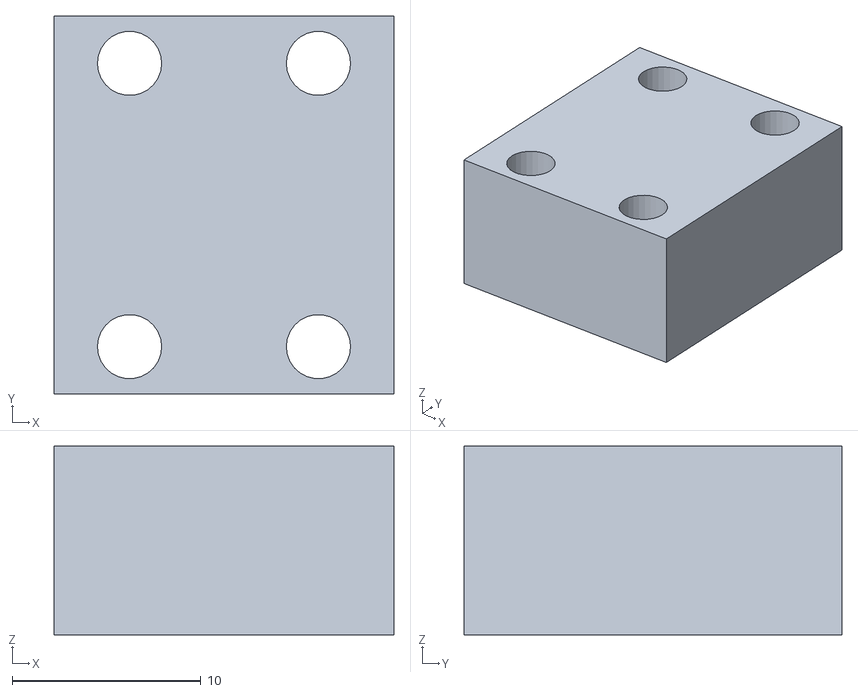
[picture p86: CAD file, 2021-10-03]
freecad/simplePnP/rehausseur.obj
18.0 x 20.0 x 10.0
