lthimx/pnpbox1/freecad/simplePnP/belt_clamp_general.FCStd

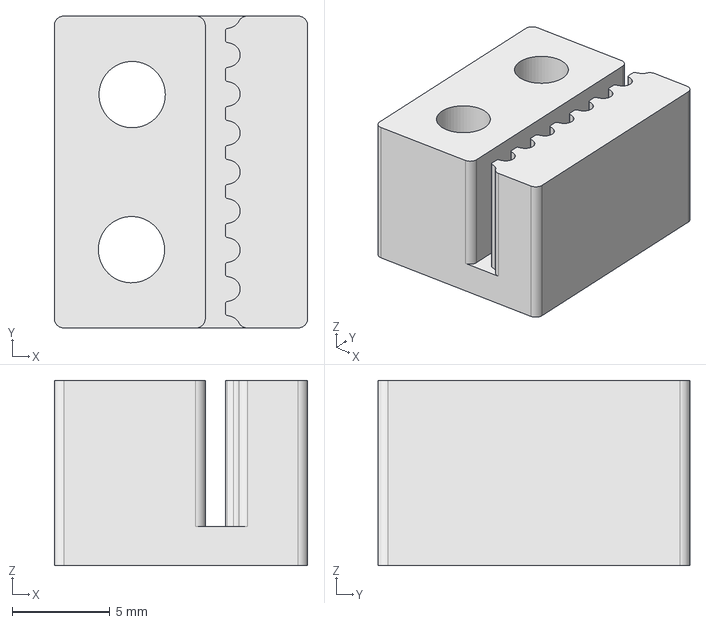
[picture p87: CAD file, 2021-10-03]
freecad/simplePnP/belt_clamp_general.FCStd
13.0 x 16.0 x 9.50 mm
