lthimx/pnpbox1/freecad/simplePnP/arduino_vis_support_dessou.obj

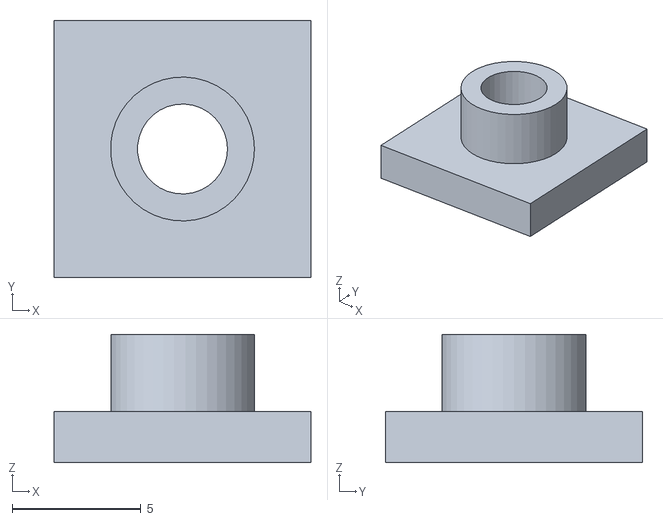
[picture p88: CAD file, 2021-10-03]
freecad/simplePnP/arduino_vis_support_dessou.obj
10.0 x 10.0 x 5.00
