lthimx/pnpbox1/freecad/simplePnP/support.FCStd

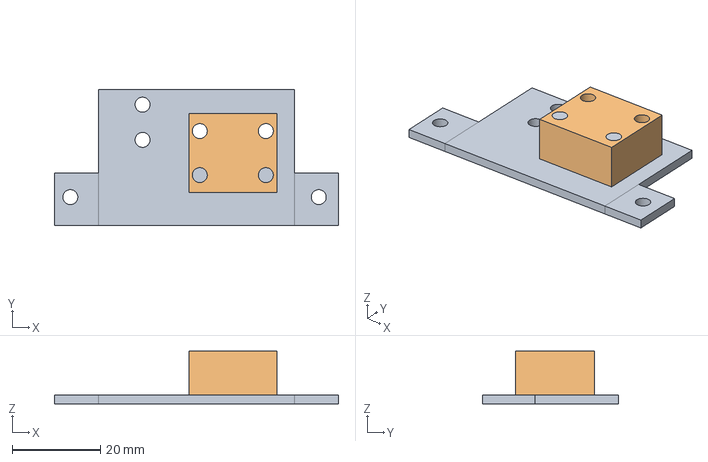
[picture p89: CAD file, 2021-10-03]
freecad/simplePnP/support.FCStd
64.5 x 31.0 x 12.0 mm
