lthimx/pnpbox1/freecad/simplePnP/bute_Y_botom.obj

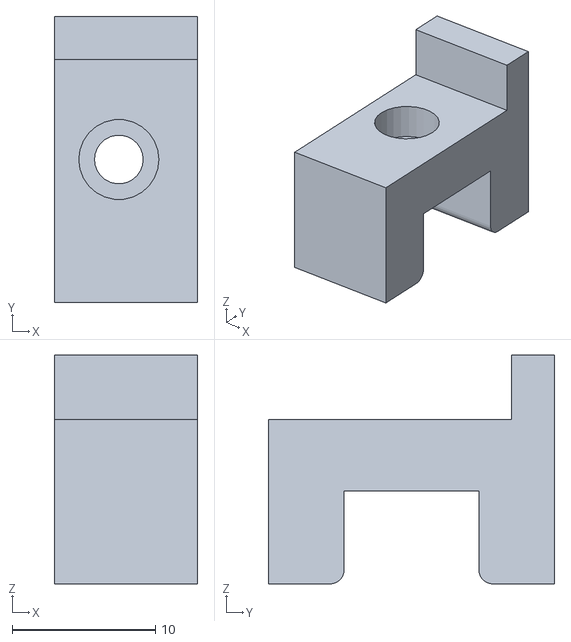
[picture p90: CAD file, 2021-10-03]
freecad/simplePnP/bute_Y_botom.obj
10.0 x 20.0 x 16.0
