lthimx/pnpbox1/freecad/simplePnP/support_nema8_vis.FCStd

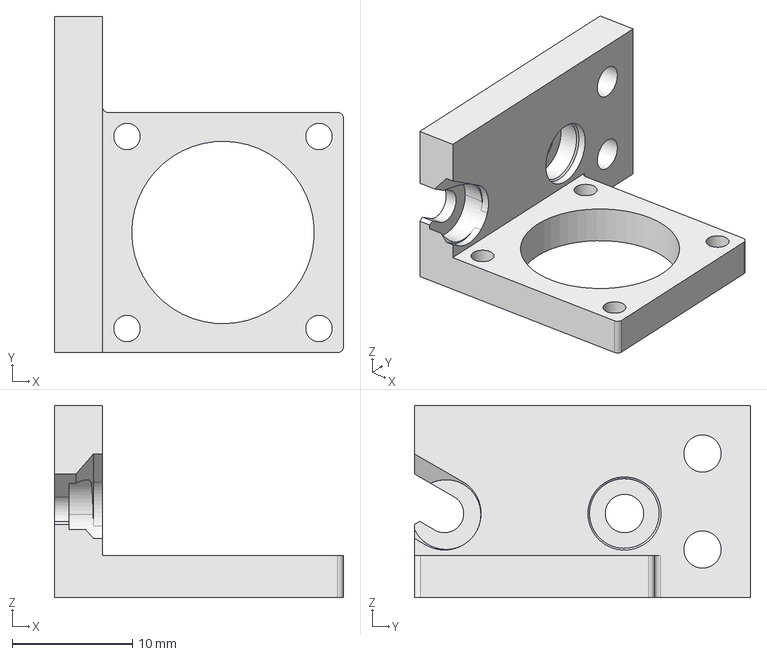
[picture p91: CAD file, 2021-10-03]
freecad/simplePnP/support_nema8_vis.FCStd
24.1 x 28.0 x 16.0 mm
