lthimx/pnpbox1/freecad/simplePnP/support4_right.obj

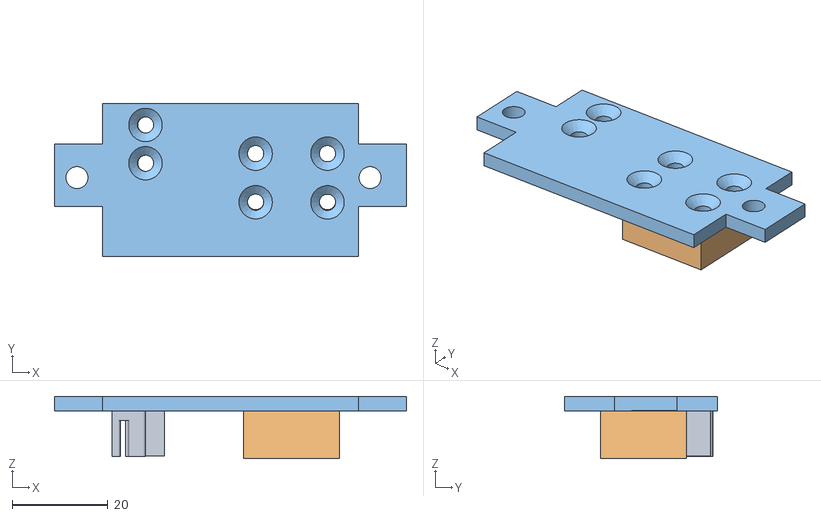
[picture p92: CAD file, 2021-10-03]
freecad/simplePnP/support4_right.obj
73.5 x 32.0 x 13.0
