lthimx/pnpbox1/freecad/simplePnP/end_course_Y_right.FCStd

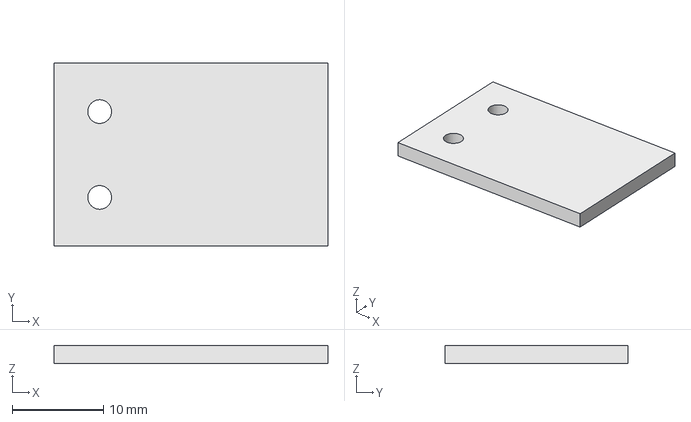
[picture p93: CAD file, 2021-10-03]
freecad/simplePnP/end_course_Y_right.FCStd
30.0 x 20.0 x 2.00 mm
