lthimx/pnpbox1/freecad/simplePnP/support_rail3.obj

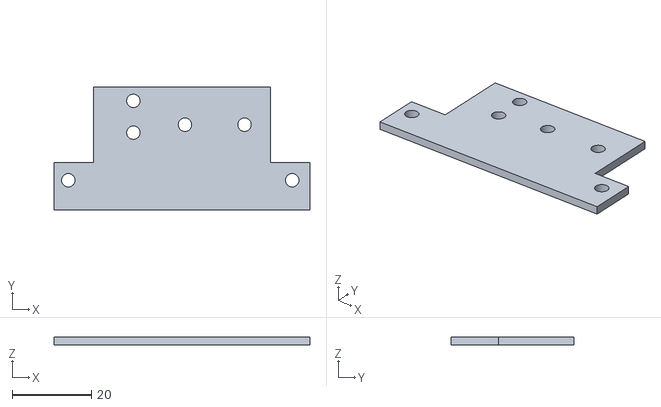
[picture p94: CAD file, 2021-10-03]
freecad/simplePnP/support_rail3.obj
64.5 x 31.0 x 2.00
