lthimx/pnpbox1/freecad/simplePnP/support_pump.FCStd

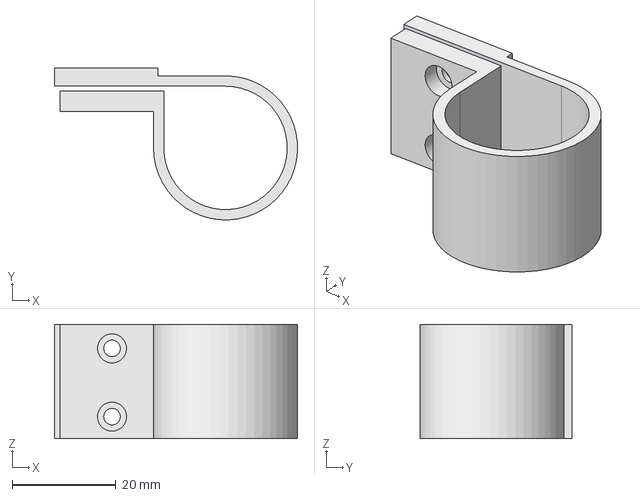
[picture p95: CAD file, 2021-10-03]
freecad/simplePnP/support_pump.FCStd
46.9 x 29.3 x 22.0 mm
