lthimx/pnpbox1/freecad/simplePnP/support_clavier.FCStd

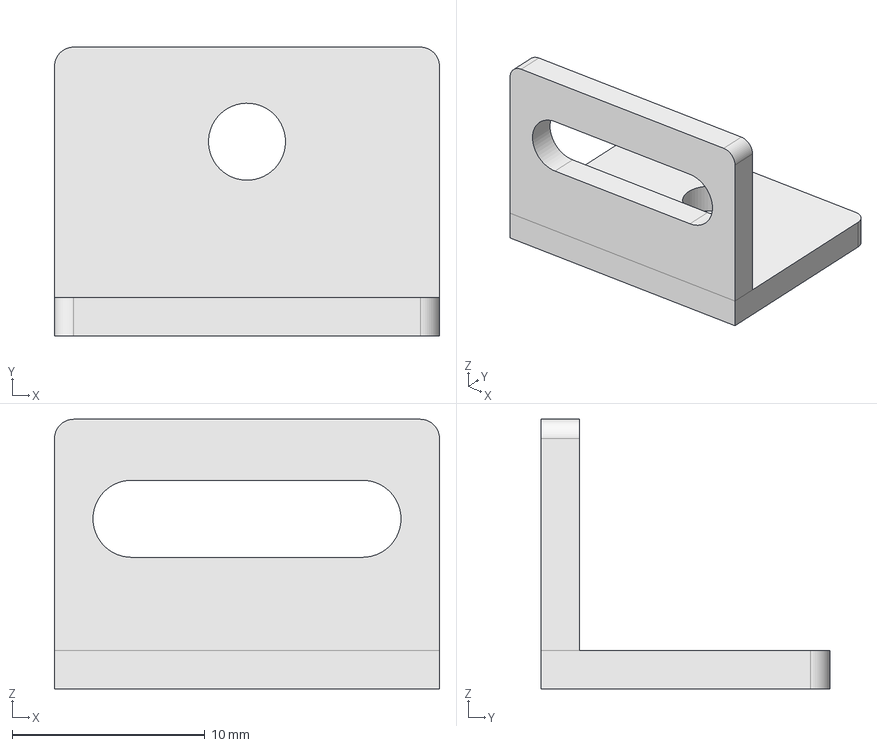
[picture p96: CAD file, 2021-10-03]
freecad/simplePnP/support_clavier.FCStd
20.0 x 15.0 x 14.0 mm
