lthimx/pnpbox1/freecad/simplePnP/support_advanced_right.FCStd

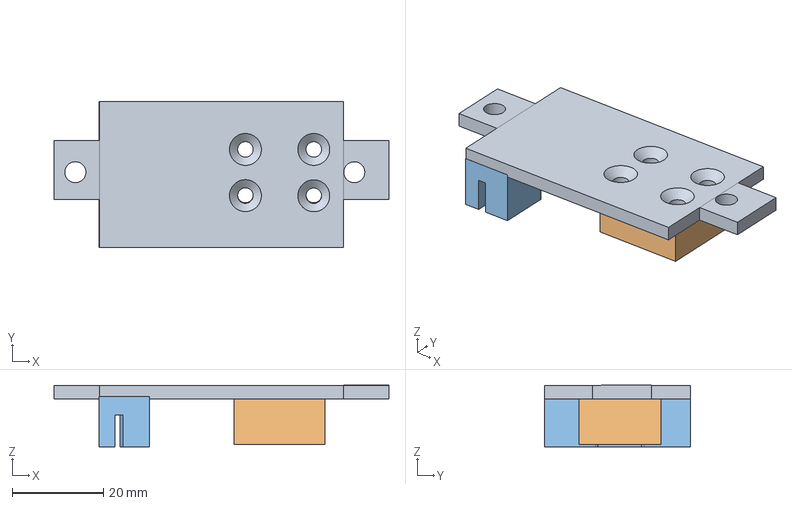
[picture p97: CAD file, 2021-10-03]
freecad/simplePnP/support_advanced_right.FCStd
73.5 x 32.0 x 13.5 mm
