lthimx/pnpbox1/freecad/simplePnP/support_rail2.obj

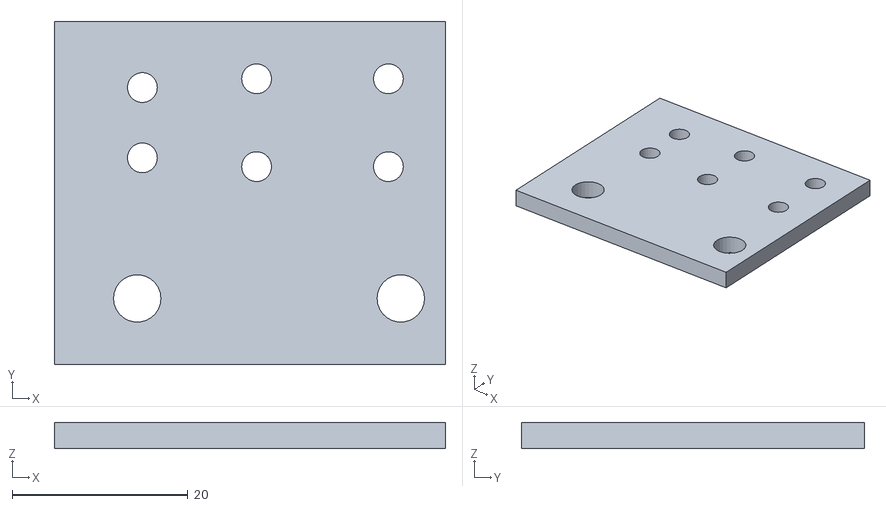
[picture p98: CAD file, 2021-10-03]
freecad/simplePnP/support_rail2.obj
44.5 x 39.0 x 3.00
