lthimx/pnpbox1/freecad/simplePnP/cam_vision_support.FCStd

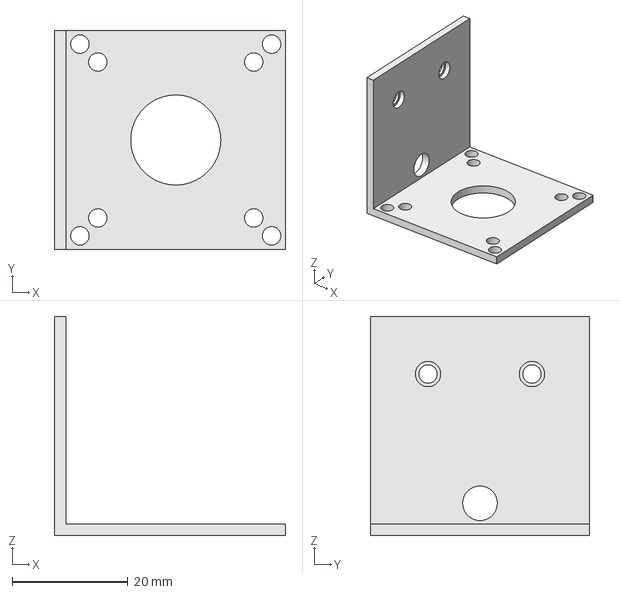
[picture p99: CAD file, 2021-10-03]
freecad/simplePnP/cam_vision_support.FCStd
40.0 x 38.0 x 38.0 mm
