lthimx/pnpbox1/freecad/simplePnP/connectique_air_tubing.obj

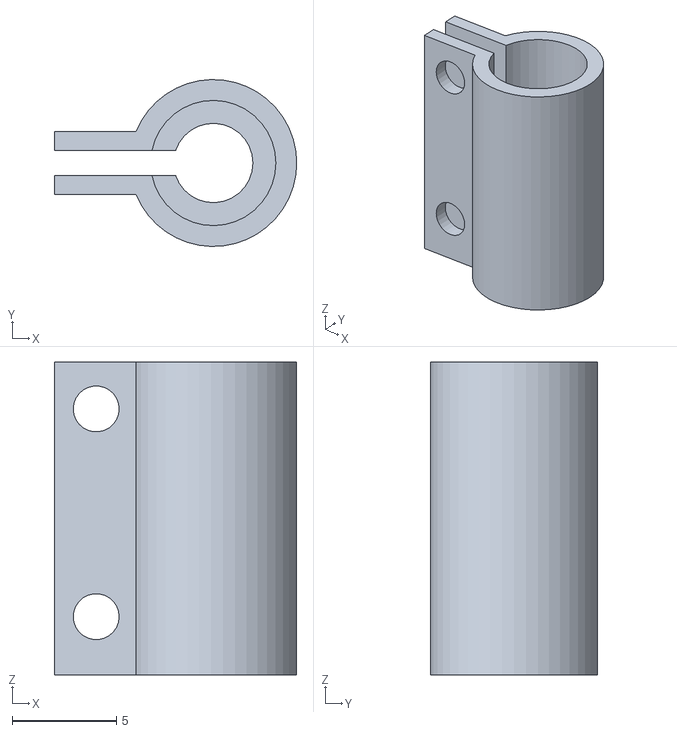
[picture p100: CAD file, 2021-10-03]
freecad/simplePnP/connectique_air_tubing.obj
11.6 x 8.00 x 15.0
