lthimx/pnpbox1/freecad/simplePnP/arduino_vis_support.FCStd

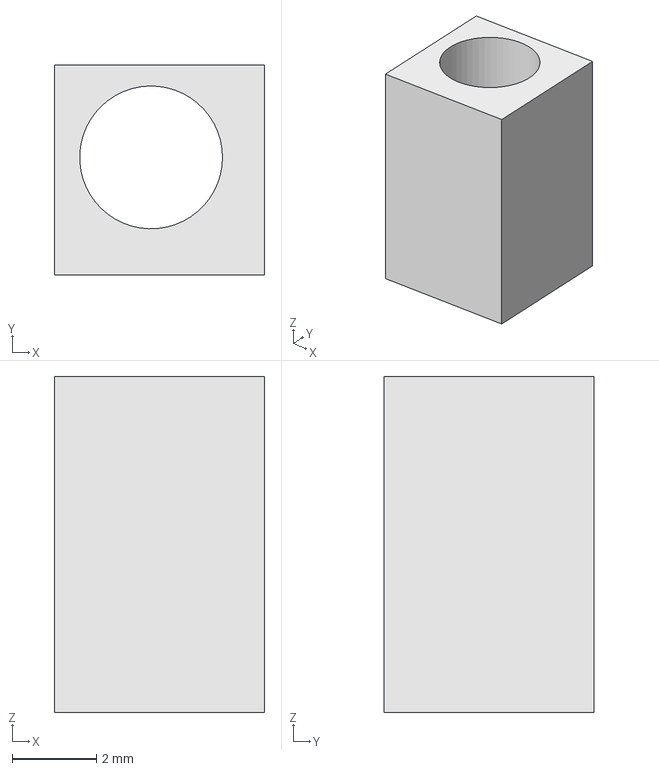
[picture p101: CAD file, 2021-10-03]
freecad/simplePnP/arduino_vis_support.FCStd
5.00 x 5.00 x 8.00 mm
