lthimx/pnpbox1/freecad/simplePnP/support4_right_tmp.obj

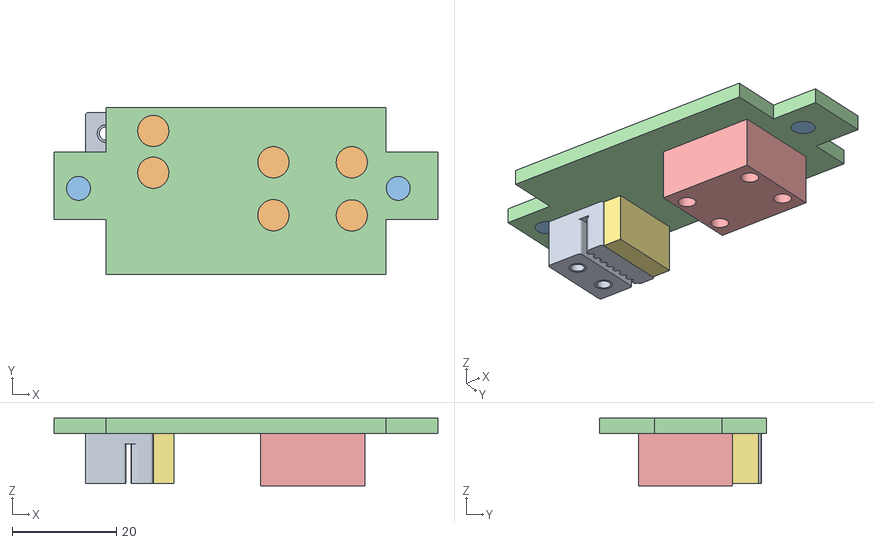
[picture p102: CAD file, 2021-10-03]
freecad/simplePnP/support4_right_tmp.obj
73.5 x 32.0 x 13.0
Hole
BaseFeature
