lthimx/pnpbox1/freecad/simplePnP/bute_3.FCStd

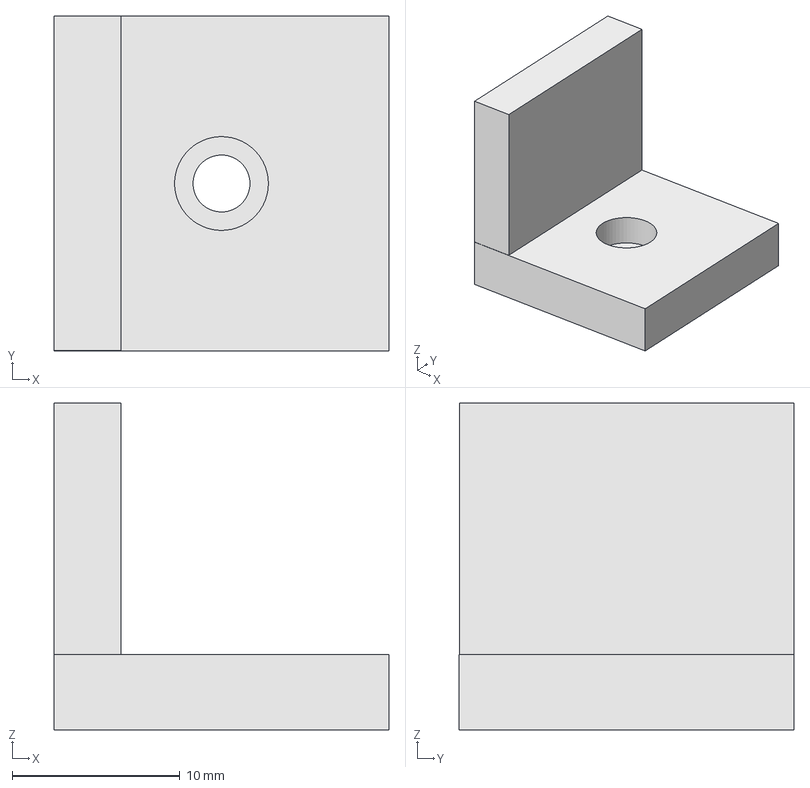
[picture p103: CAD file, 2021-10-03]
freecad/simplePnP/bute_3.FCStd
20.0 x 20.0 x 19.5 mm
