lthimx/pnpbox1/freecad/simplePnP/adv_support_left2.obj

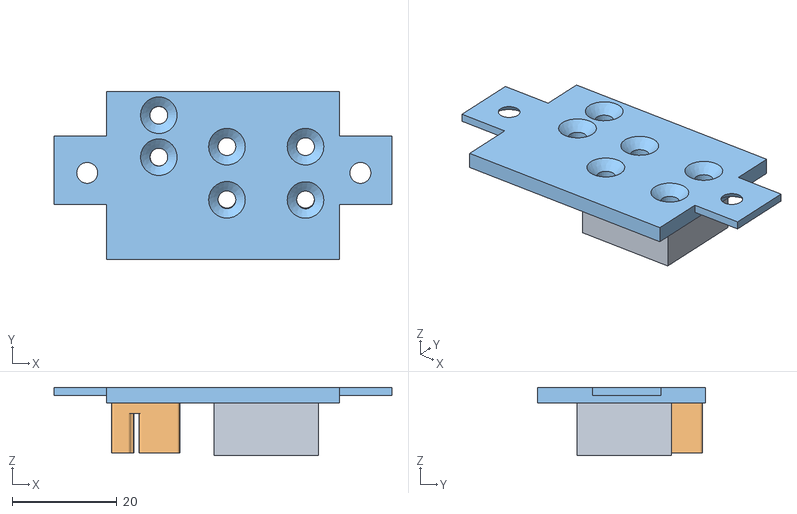
[picture p104: CAD file, 2021-10-03]
freecad/simplePnP/adv_support_left2.obj
64.5 x 32.0 x 13.0
