lthimx/pnpbox1/freecad/simplePnP/end_course_actuator_2.FCStd

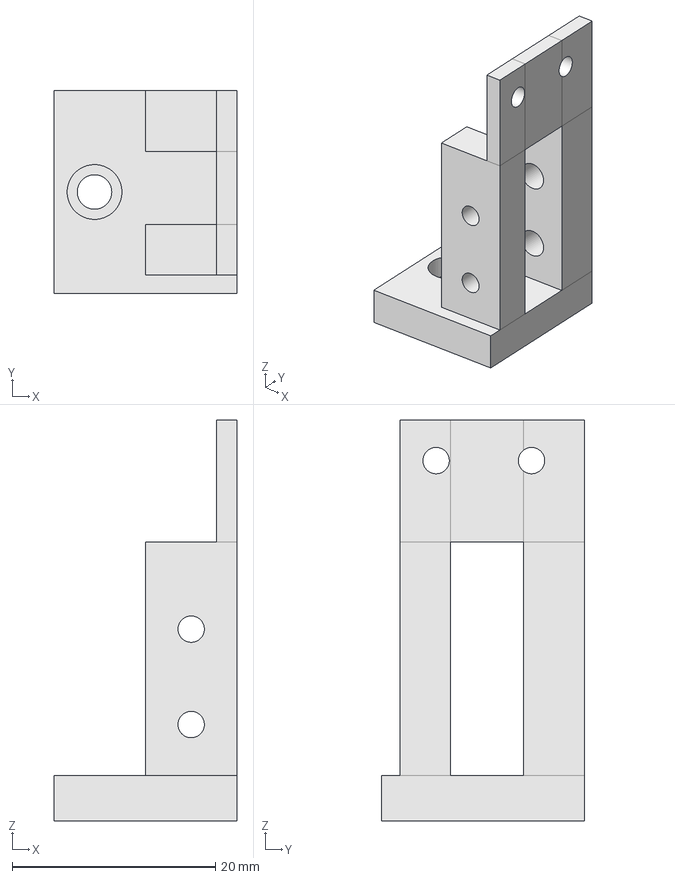
[picture p105: CAD file, 2021-10-03]
freecad/simplePnP/end_course_actuator_2.FCStd
18.0 x 20.0 x 39.5 mm
