lthimx/pnpbox1/freecad/simplePnP/ajust_drag_chain.obj

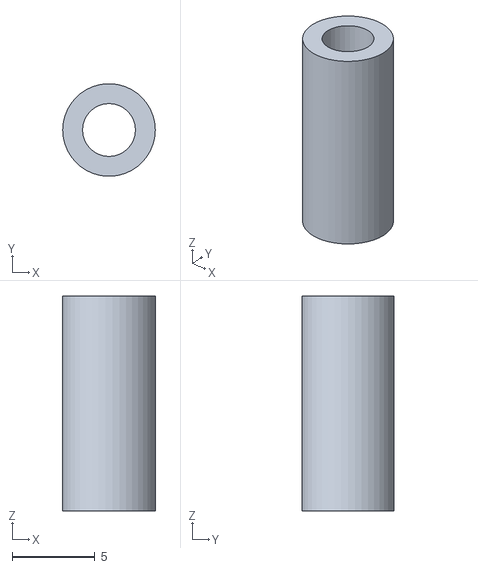
[picture p106: CAD file, 2021-10-03]
freecad/simplePnP/ajust_drag_chain.obj
5.60 x 5.58 x 13.0
