lthimx/pnpbox1/freecad/simplePnP/poulie_support_XXX.FCStd

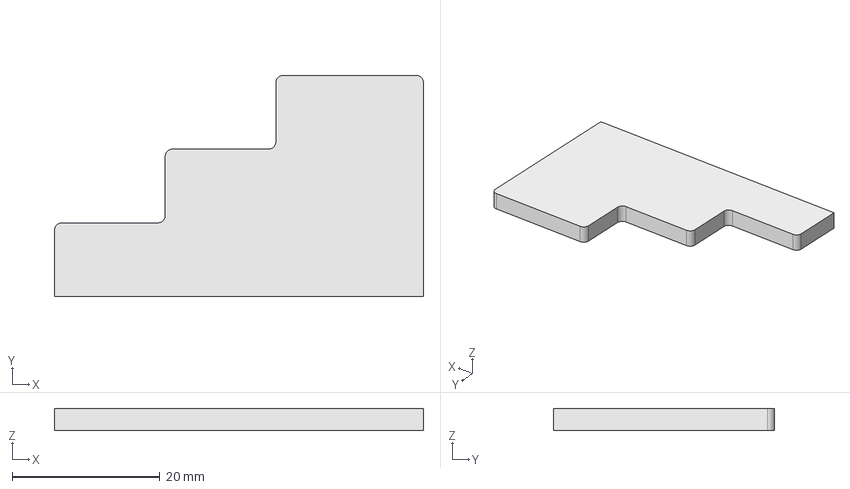
[picture p107: CAD file, 2021-10-03]
freecad/simplePnP/poulie_support_XXX.FCStd
50.0 x 30.0 x 3.00 mm
