lthimx/pnpbox1/freecad/simplePnP/belt_clamp_general_right.FCStd

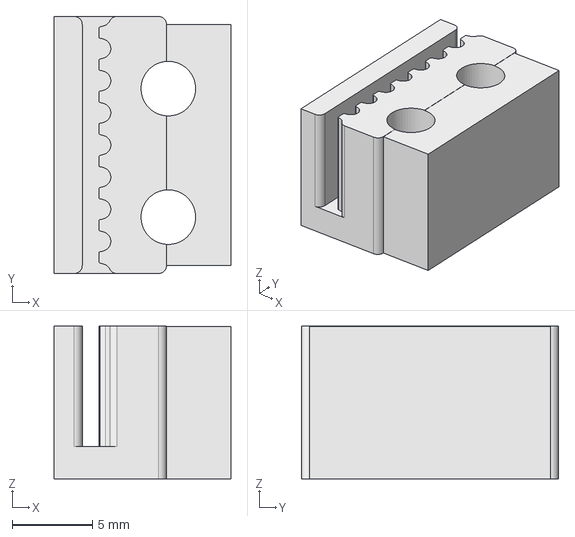
[picture p108: CAD file, 2021-10-03]
freecad/simplePnP/belt_clamp_general_right.FCStd
11.0 x 16.0 x 9.50 mm
